Green-Software-Foundation/open19/chapters/book/appendix.adoc

ifndef::imagesdir[:imagesdir: ../../images]

[Appendix]

= Data connector pin assignments

[#table-data-connector-pin-assignments]
.Data connector pin assignments


{sp} +

ifdef::private[]

== Private Appendix

The following material is included for the convenience of Open19 members only. No redistribution to the public is permitted.

=== Data connector sales drawing
[#Molex-Impel-sales-drawing]
.Molex Impel 4x8 Sales Drawing


{sp} +

=== Power connector sales drawing
[#Molex-Ten60-sales-drawing]
.Molex Ten60 Sales DRawing


{sp} +
ifdef::liquid[]
=== Liquid connector spec sheet
[#cpc-blq4-part]
.CPC BLQ4 Spec Sheet


{sp} +

[#cpc-blq6-part]
.CPC BLQ6 Spec Sheet


{sp} +
endif::[]
endif::[]
