Green-Software-Foundation/open19/cooling/single_phase/Max_velocity_stainless.png

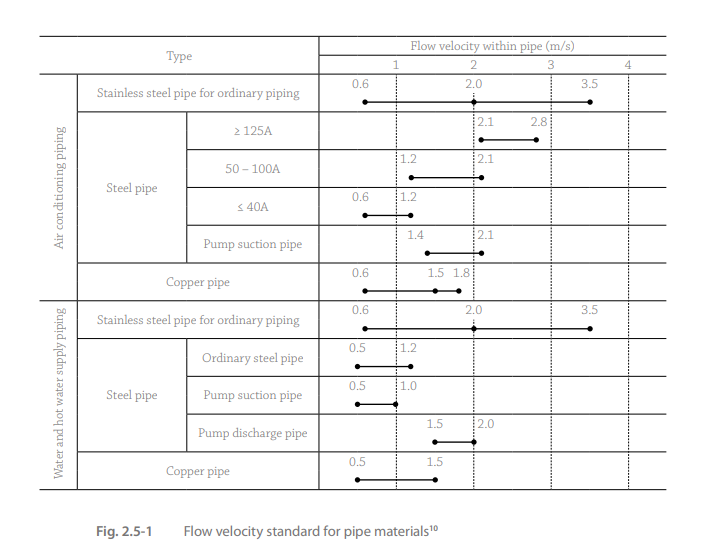
cooling/single_phase/Max_velocity_stainless.png
