Green-Software-Foundation/open19/images/chapters/ch_brick_mechanical/dhdw_brick_mechanical_stop.png

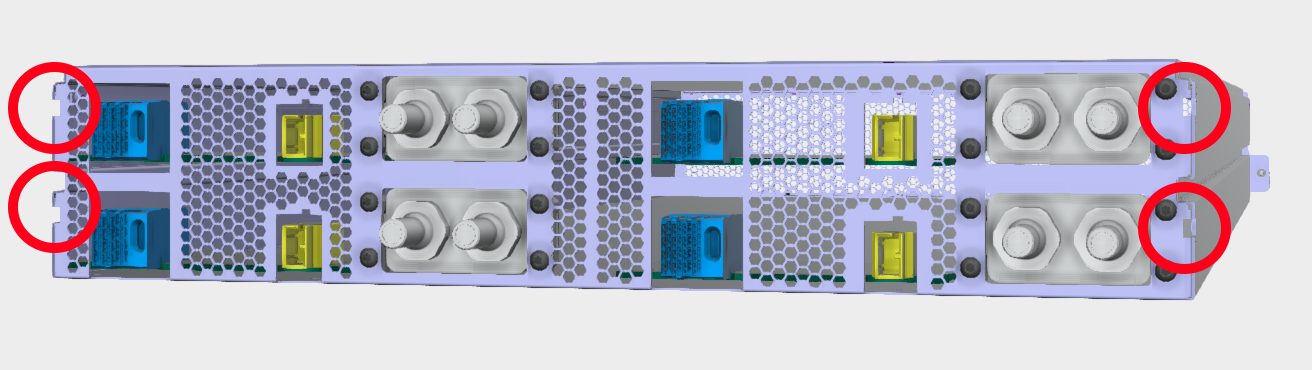
images/chapters/ch_brick_mechanical/dhdw_brick_mechanical_stop.png
