Green-Software-Foundation/open19/images/chapters/ch_brick_mechanical/dhdw_brick_pcb_dimensions.png

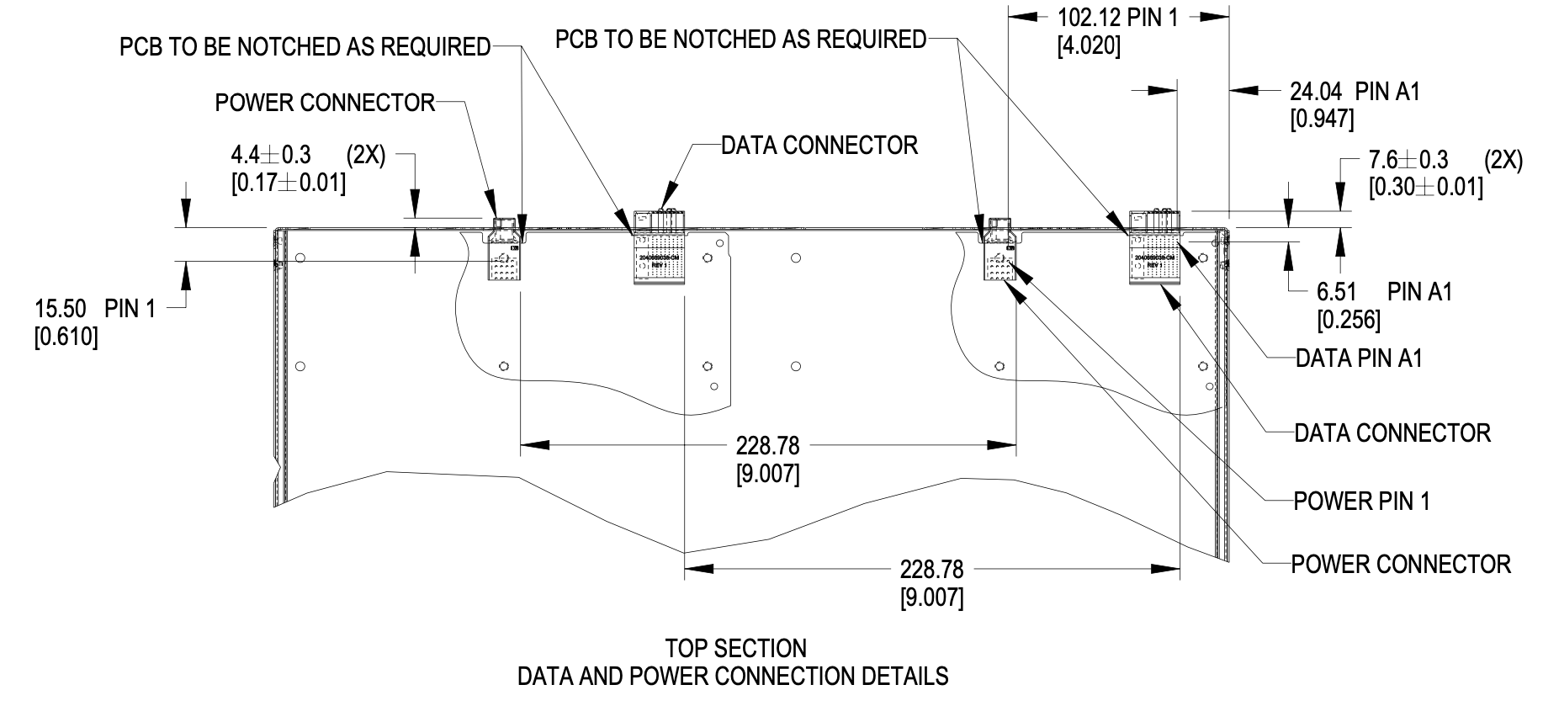
images/chapters/ch_brick_mechanical/dhdw_brick_pcb_dimensions.png
