Green-Software-Foundation/open19/images/chapters/ch_brick_mechanical/dhhw_brick_retention.png

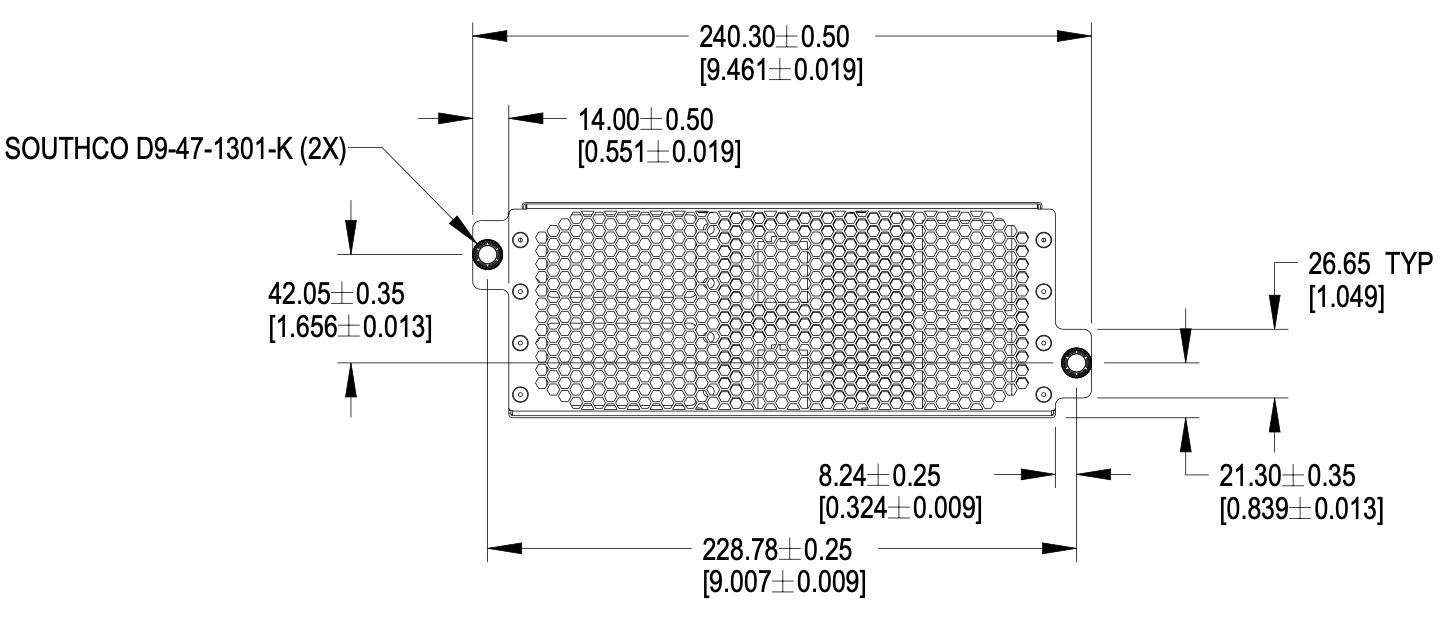
images/chapters/ch_brick_mechanical/dhhw_brick_retention.png
