Green-Software-Foundation/open19/images/chapters/ch_brick_mechanical/shdw_brick_keepout_zone.png

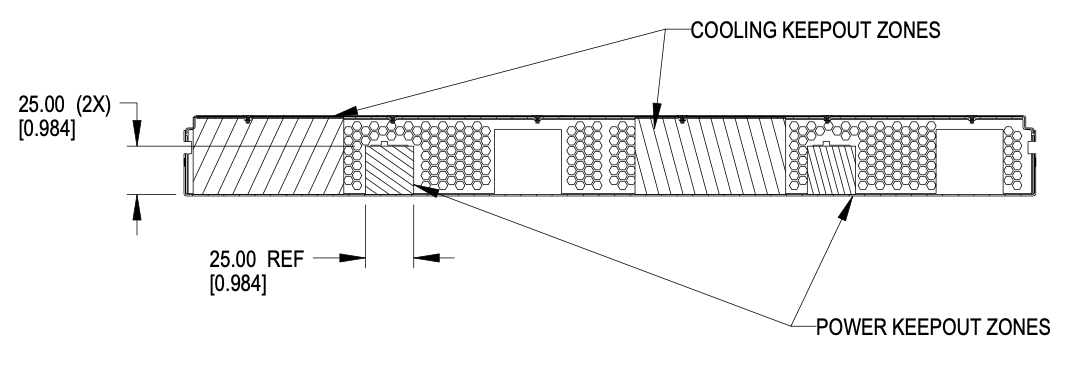
images/chapters/ch_brick_mechanical/shdw_brick_keepout_zone.png
