Green-Software-Foundation/open19/images/chapters/ch_brick_mechanical/shdw_brick_keepout_zone_top.png

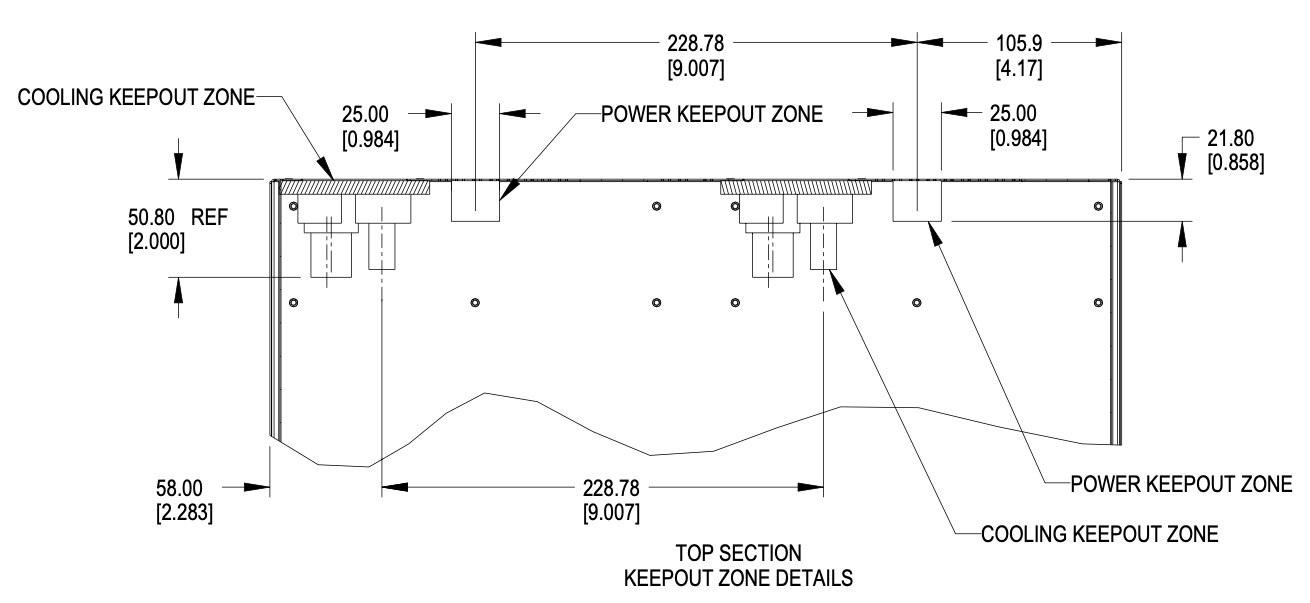
images/chapters/ch_brick_mechanical/shdw_brick_keepout_zone_top.png
