Green-Software-Foundation/open19/images/chapters/ch_brick_mechanical/shdw_brick_keying_dimensions.png

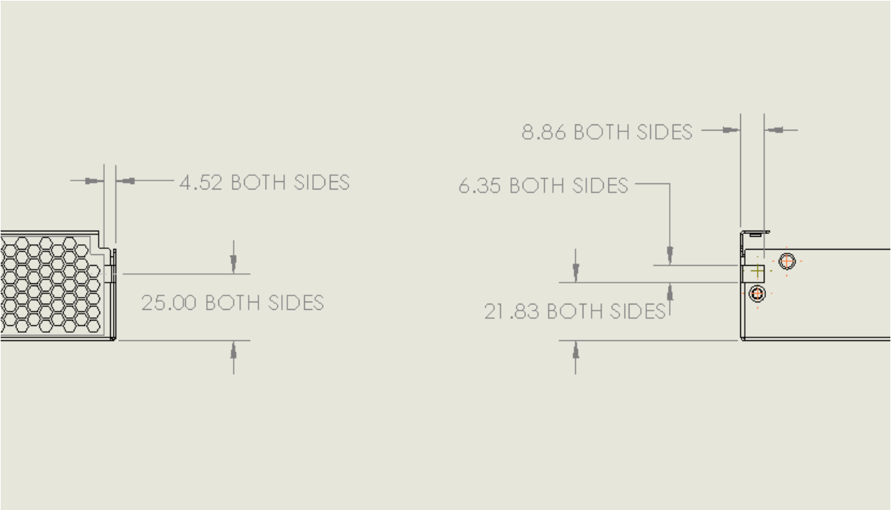
images/chapters/ch_brick_mechanical/shdw_brick_keying_dimensions.png
