Green-Software-Foundation/open19/images/chapters/ch_system_architecture/8rucagefront.png

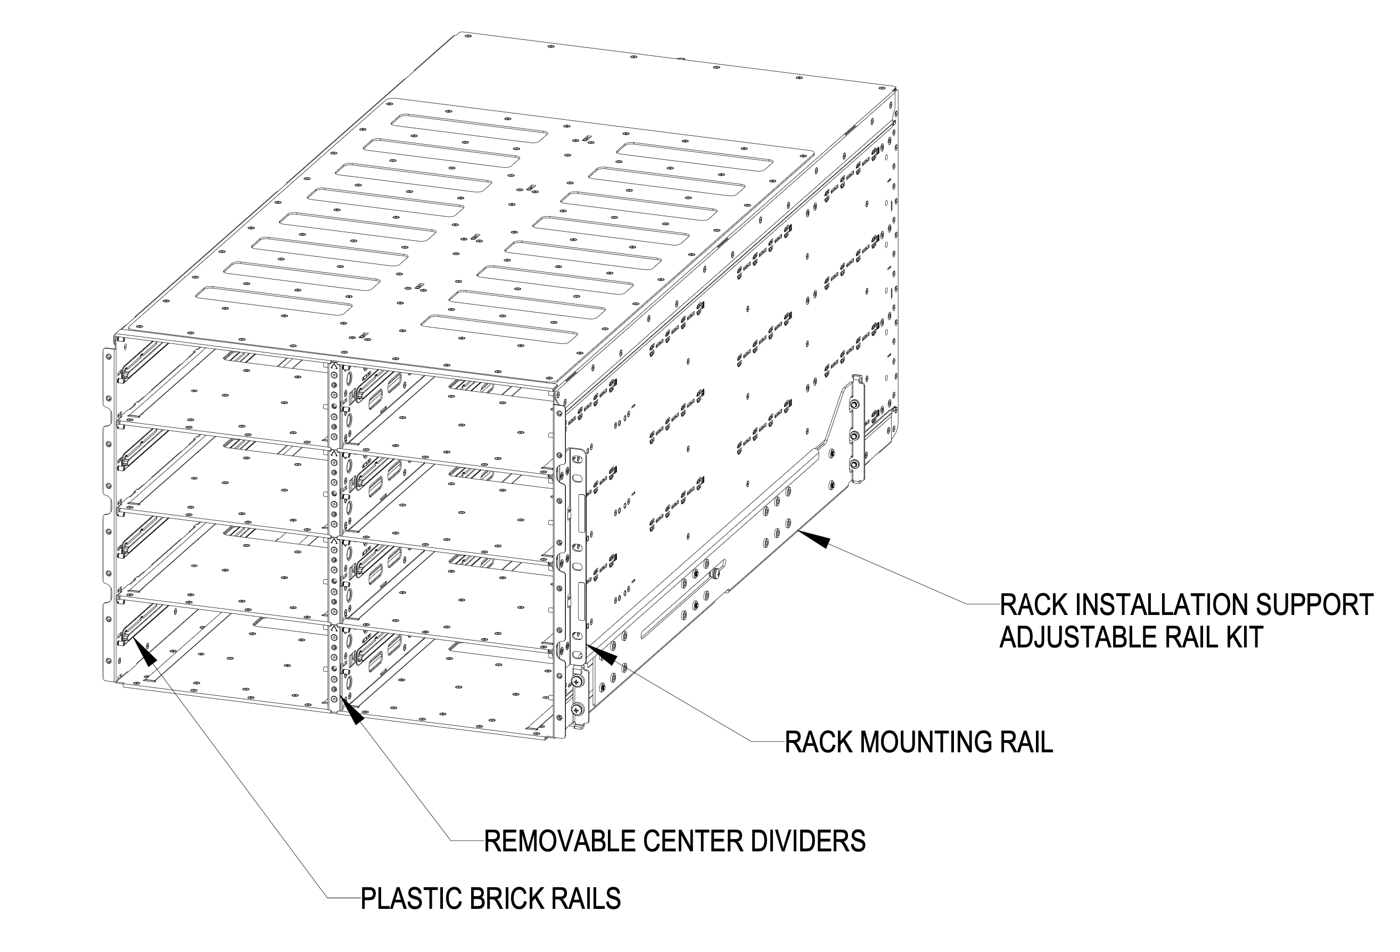
images/chapters/ch_system_architecture/8rucagefront.png
