Green-Software-Foundation/open19/images/chapters/ch_system_architecture/bracket_sample_right.png

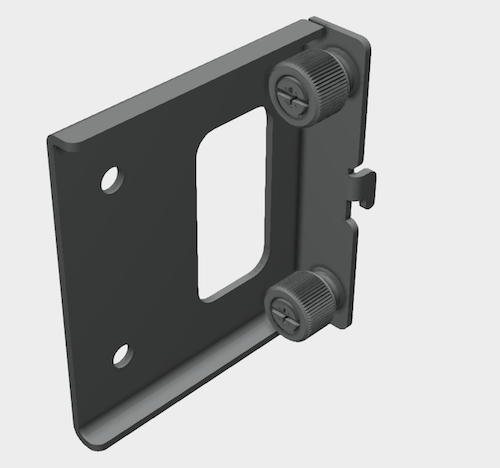
images/chapters/ch_system_architecture/bracket_sample_right.png
