Green-Software-Foundation/open19/images/chapters/ch_system_architecture/cagepaneldetail.png

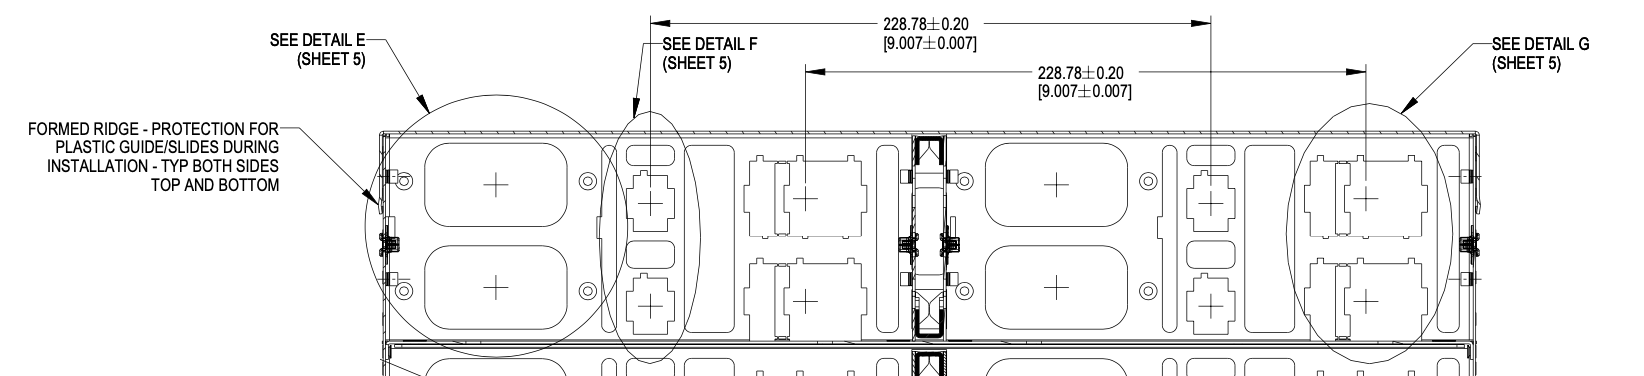
images/chapters/ch_system_architecture/cagepaneldetail.png
