Green-Software-Foundation/open19/images/chapters/ch_system_architecture/center_divider.png

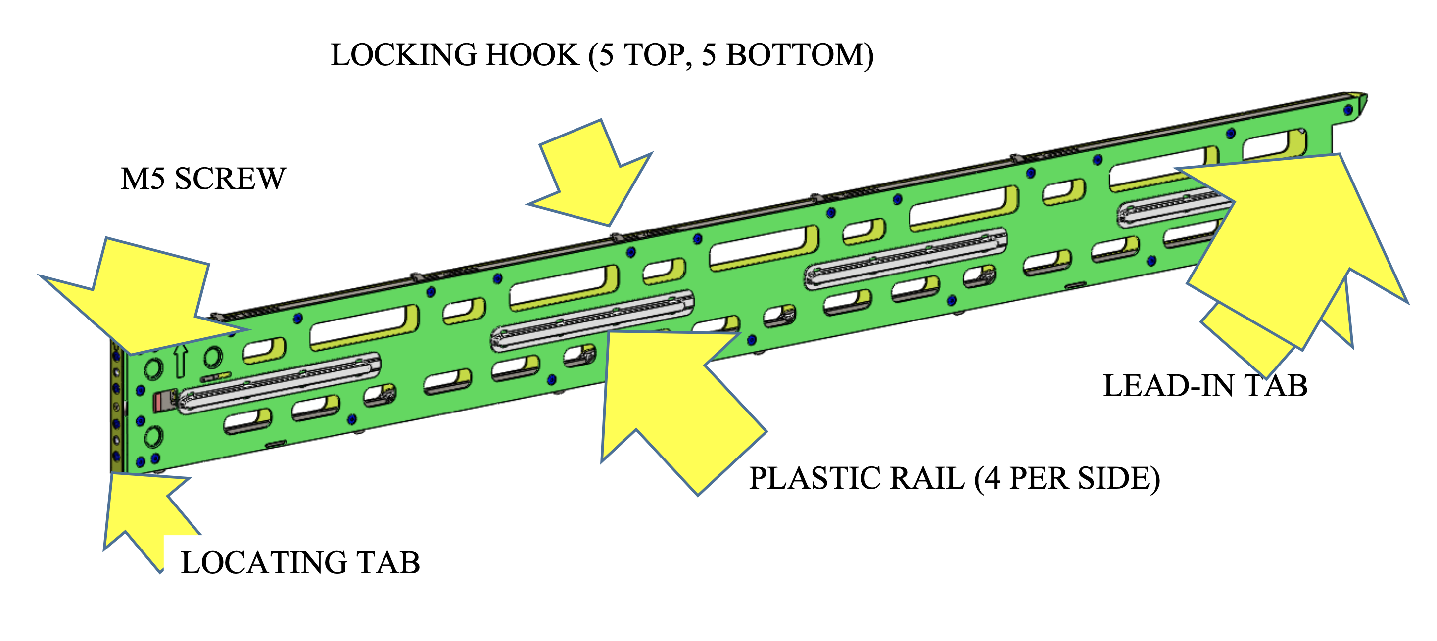
images/chapters/ch_system_architecture/center_divider.png
