Green-Software-Foundation/open19/images/chapters/ch_system_architecture/Coeur_power_shelf_connector.png

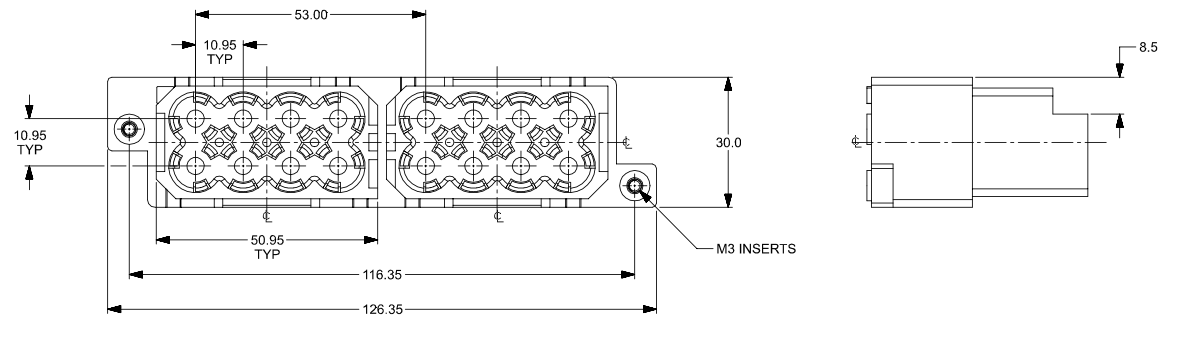
images/chapters/ch_system_architecture/Coeur_power_shelf_connector.png
