Green-Software-Foundation/open19/images/chapters/ch_system_architecture/keying_stops.png

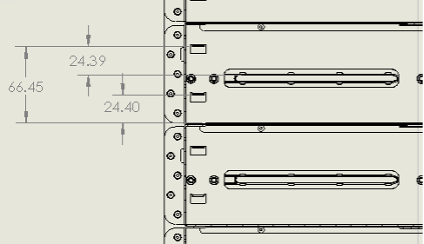
images/chapters/ch_system_architecture/keying_stops.png
