Green-Software-Foundation/open19/images/chapters/ch_system_architecture/open19_v2_cage_horizontal_divider.png

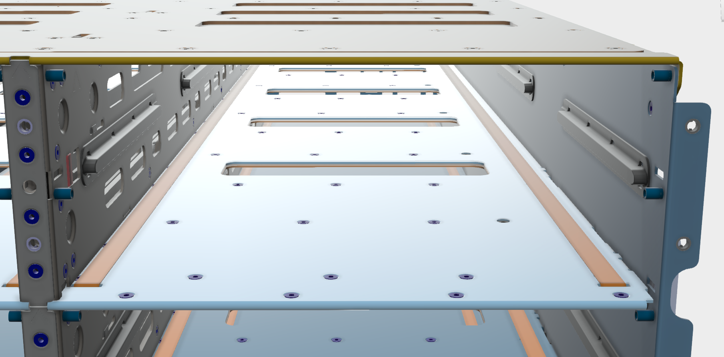
images/chapters/ch_system_architecture/open19_v2_cage_horizontal_divider.png
