Green-Software-Foundation/open19/images/ConfidentialDraft.png

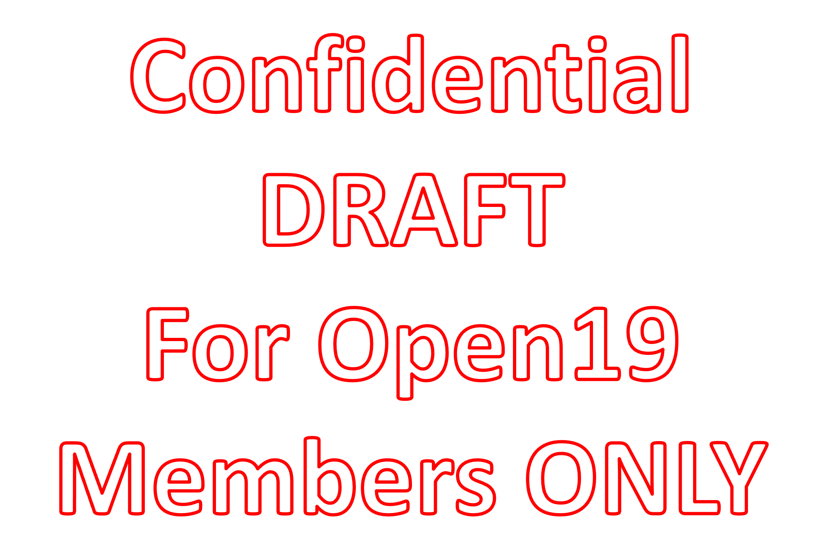
images/ConfidentialDraft.png
