Green-Software-Foundation/open19/images/cooling/single_phase/BLQ4_body.png

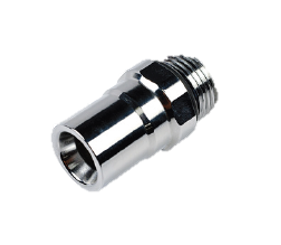
images/cooling/single_phase/BLQ4_body.png
