Green-Software-Foundation/open19/images/cooling/single_phase/BLQ4_flow_vs_dP.png

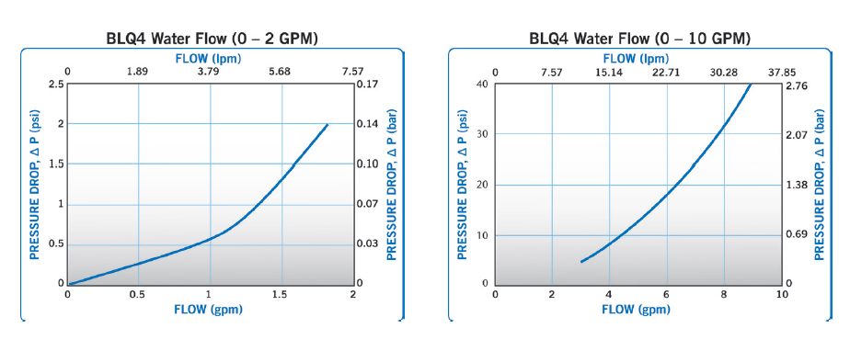
images/cooling/single_phase/BLQ4_flow_vs_dP.png
