Green-Software-Foundation/open19/images/cooling/single_phase/Body_mating_surface.jpg

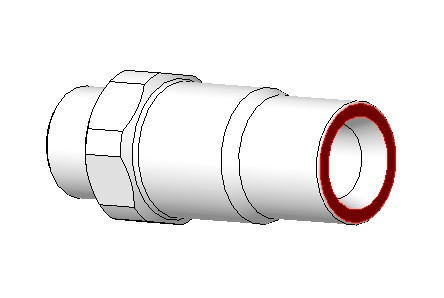
images/cooling/single_phase/Body_mating_surface.jpg
