Green-Software-Foundation/open19/images/cooling/single_phase/brick_offset_dimension.png

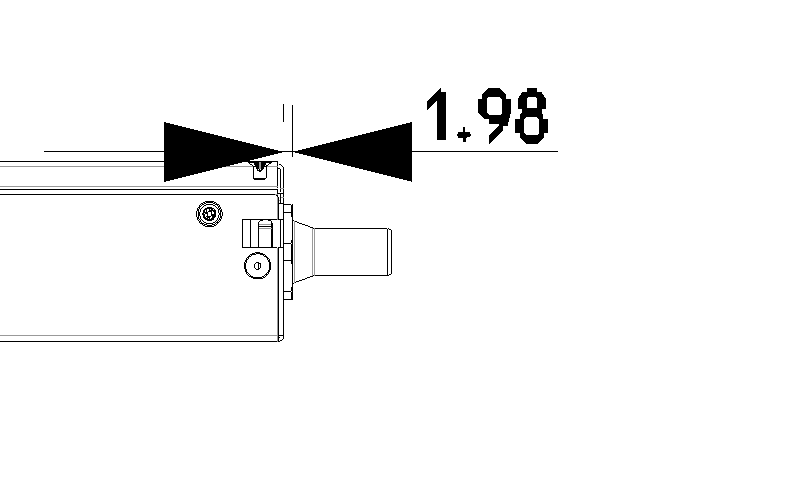
images/cooling/single_phase/brick_offset_dimension.png
