Green-Software-Foundation/open19/images/cooling/single_phase/connector_in_brick_changed_brick.png

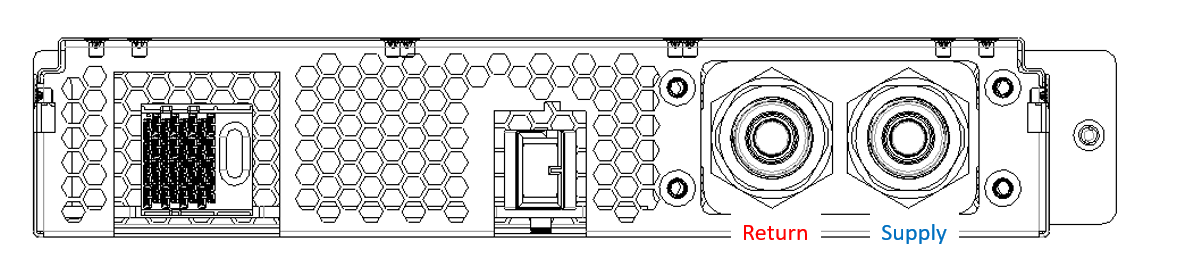
images/cooling/single_phase/connector_in_brick_changed_brick.png
