Green-Software-Foundation/open19/images/cooling/single_phase/no_offset_1p_cage_manifold.png

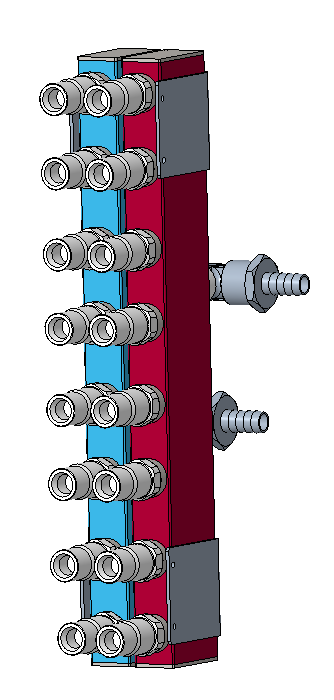
images/cooling/single_phase/no_offset_1p_cage_manifold.png
