Green-Software-Foundation/open19/images/cooling/single_phase/no_offset_brick_connector_dimension.png

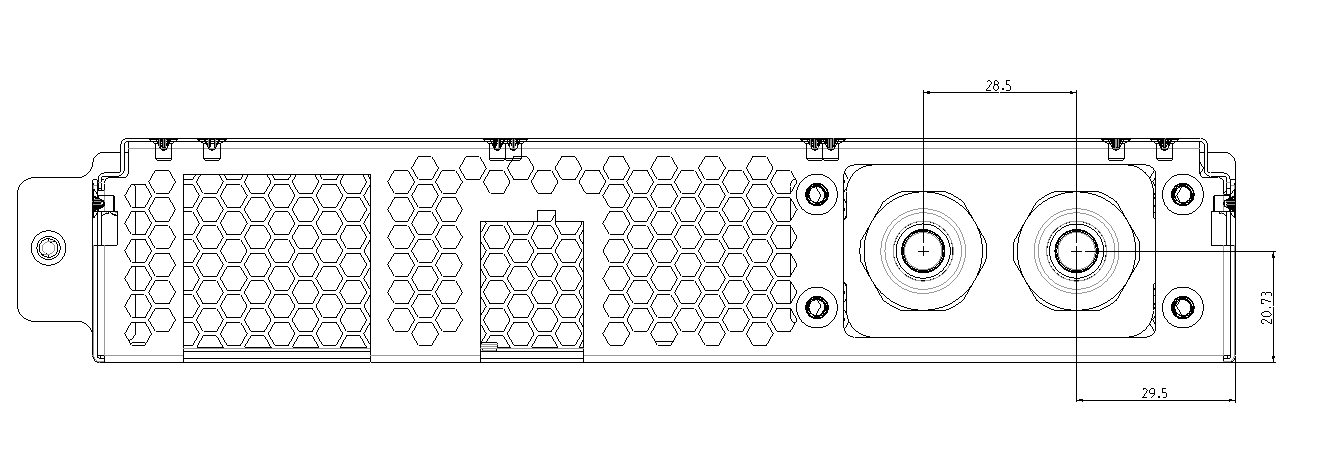
images/cooling/single_phase/no_offset_brick_connector_dimension.png
