Green-Software-Foundation/open19/images/cooling/single_phase/no_offset_brick_supply_return.png

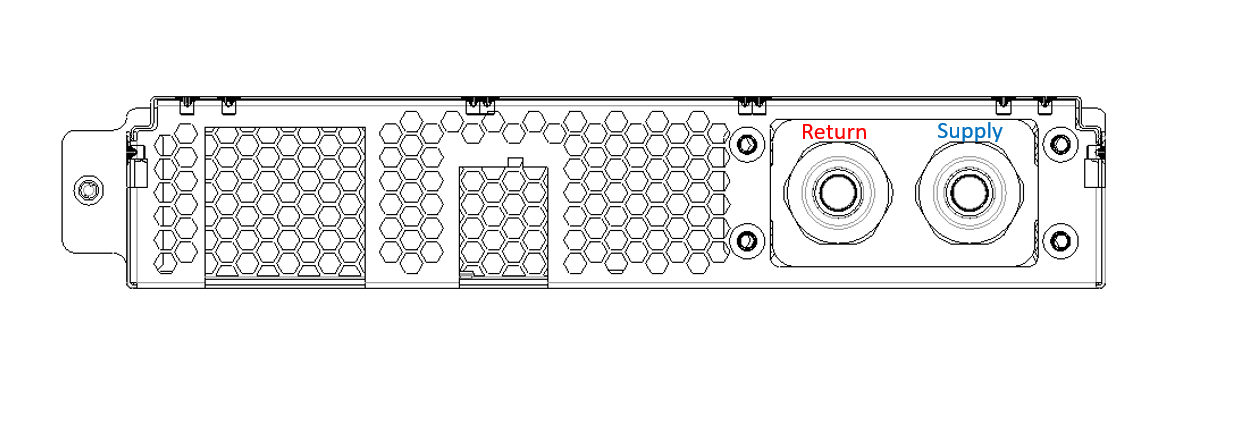
images/cooling/single_phase/no_offset_brick_supply_return.png
