Green-Software-Foundation/open19/images/cooling/single_phase/No_offset_cage_with_manifold_1pbrick.png

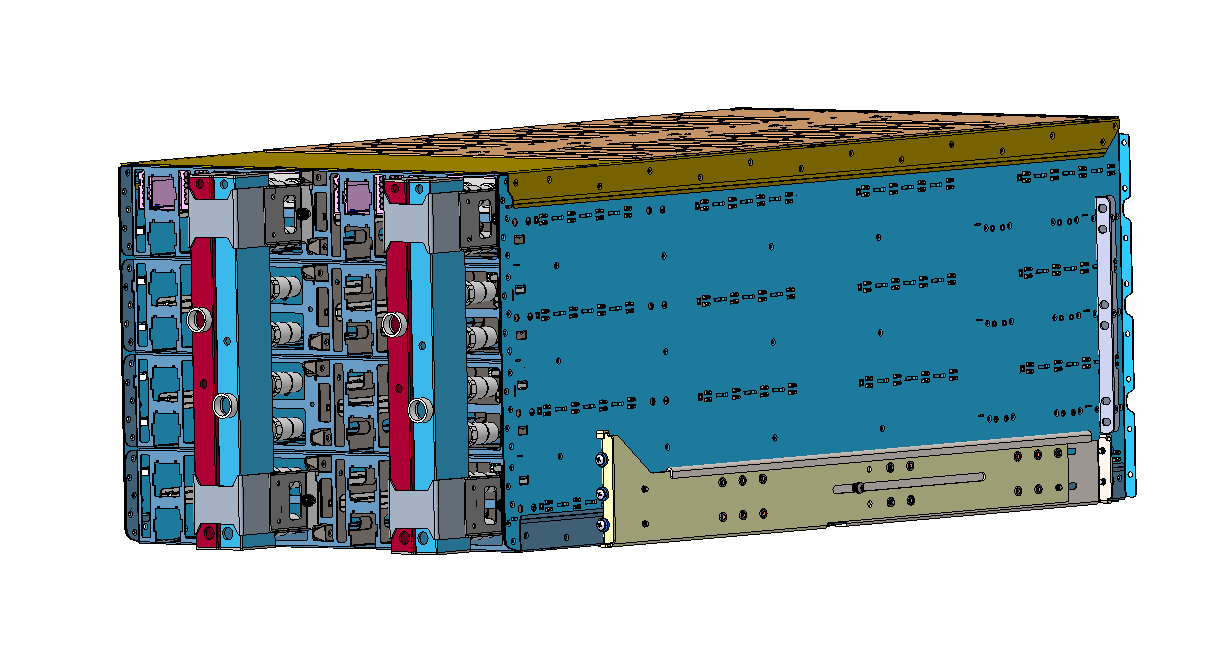
images/cooling/single_phase/No_offset_cage_with_manifold_1pbrick.png
