Green-Software-Foundation/open19/images/cooling/single_phase/no_offset_manifold_spacing.png

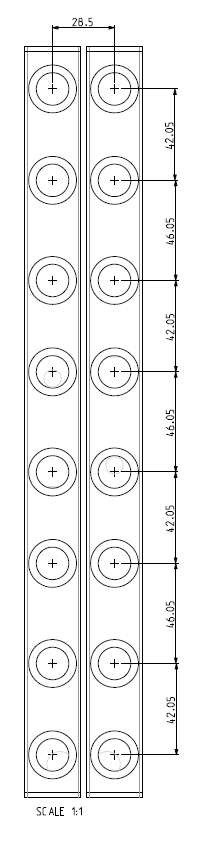
images/cooling/single_phase/no_offset_manifold_spacing.png
