Green-Software-Foundation/open19/images/cooling/single_phase/shdw_connector_in_brick.png

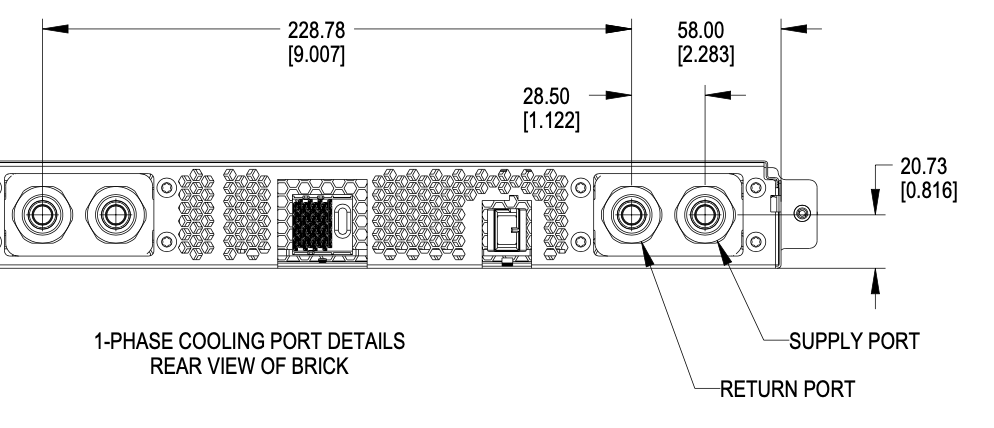
images/cooling/single_phase/shdw_connector_in_brick.png
