Green-Software-Foundation/open19/images/cooling/two_phase/dhhw_supply_return_dimensions.png

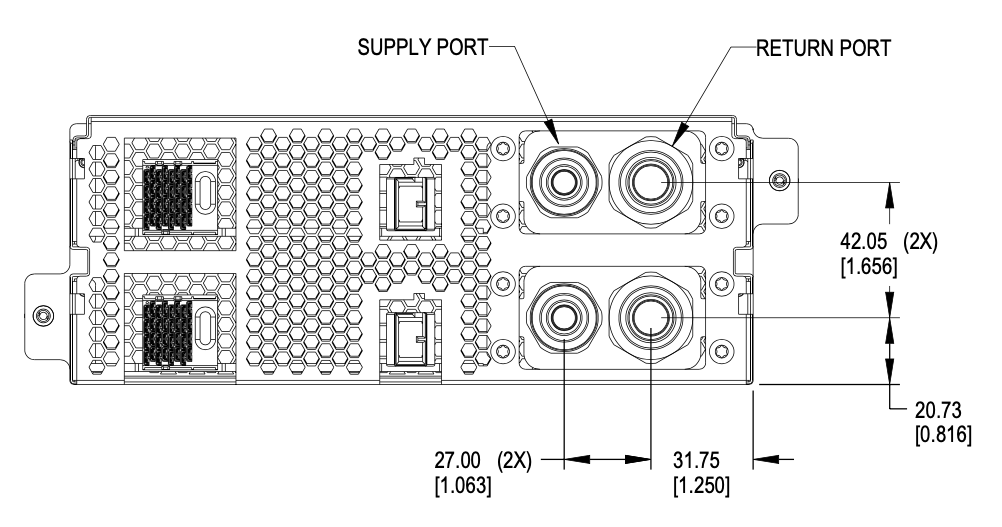
images/cooling/two_phase/dhhw_supply_return_dimensions.png
