Green-Software-Foundation/open19/images/cooling/two_phase/image1.png

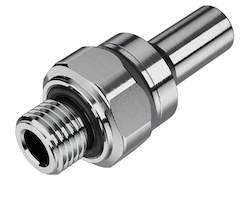
images/cooling/two_phase/image1.png
