Green-Software-Foundation/open19/images/cooling/two_phase/image3.png

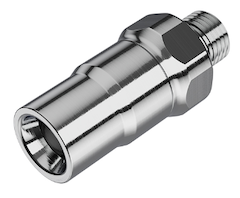
images/cooling/two_phase/image3.png
