Green-Software-Foundation/open19/images/cooling/two_phase/image5.png

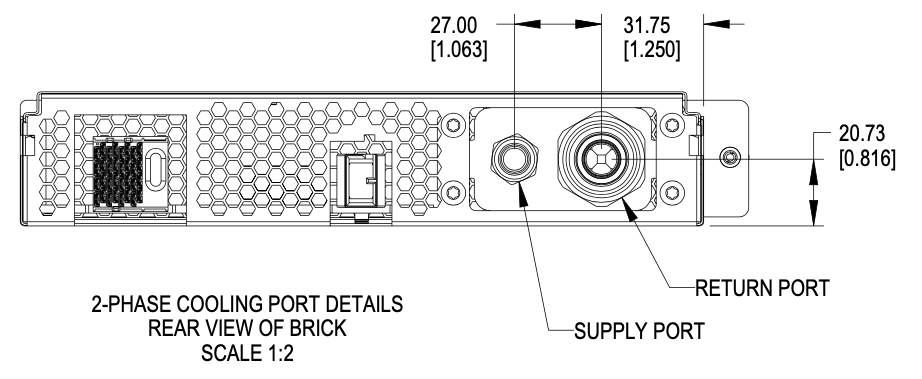
images/cooling/two_phase/image5.png
