Green-Software-Foundation/open19/images/cooling/two_phase/image8.png

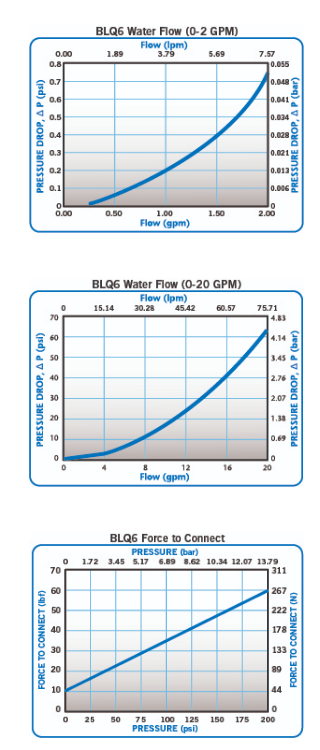
images/cooling/two_phase/image8.png
