Green-Software-Foundation/open19/images/cooling/two_phase/image9.png

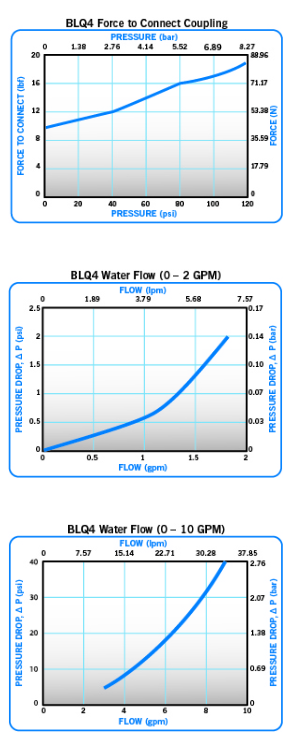
images/cooling/two_phase/image9.png
