Green-Software-Foundation/open19/images/cooling/two_phase/image10.png

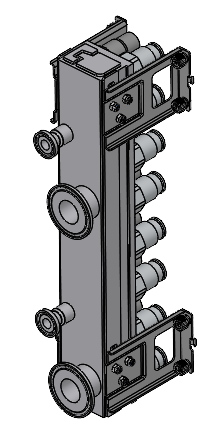
images/cooling/two_phase/image10.png
