Green-Software-Foundation/open19/images/cooling/two_phase/image11.png

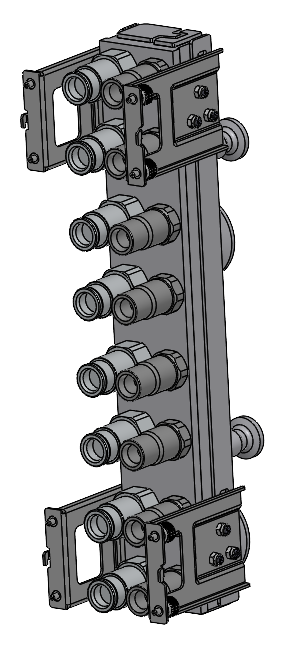
images/cooling/two_phase/image11.png
