Green-Software-Foundation/open19/images/cooling/two_phase/image12.png

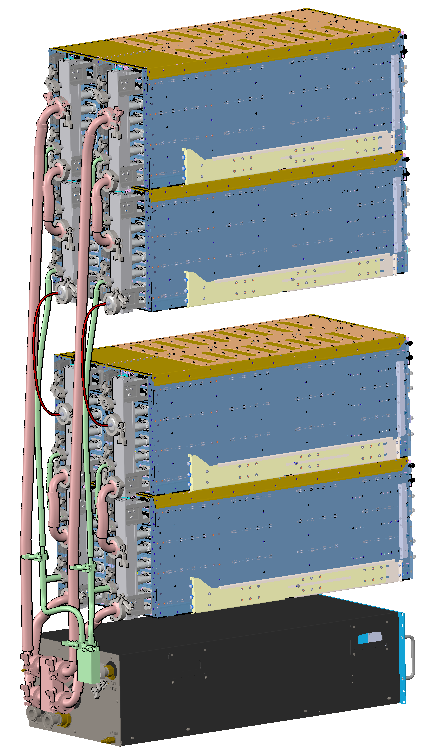
images/cooling/two_phase/image12.png
