Green-Software-Foundation/open19/images/cooling/two_phase/imagea8.png

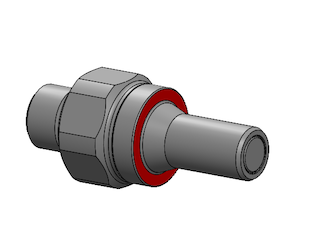
images/cooling/two_phase/imagea8.png
