Green-Software-Foundation/open19/images/cooling/two_phase/imagea9.png

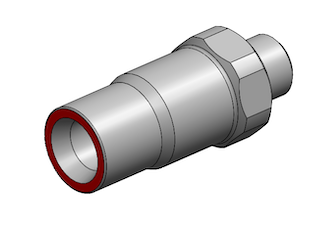
images/cooling/two_phase/imagea9.png
