Green-Software-Foundation/open19/images/cooling/two_phase/imagea11.png

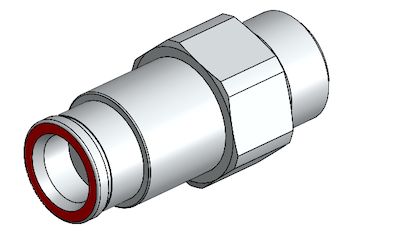
images/cooling/two_phase/imagea11.png
