Green-Software-Foundation/open19/images/cooling/two_phase/imagea12.png

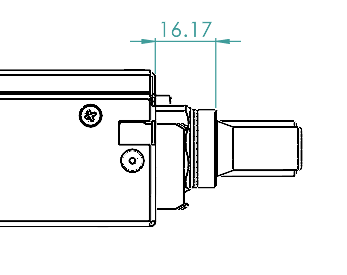
images/cooling/two_phase/imagea12.png
