Green-Software-Foundation/open19/images/cooling/two_phase/imagea13.png

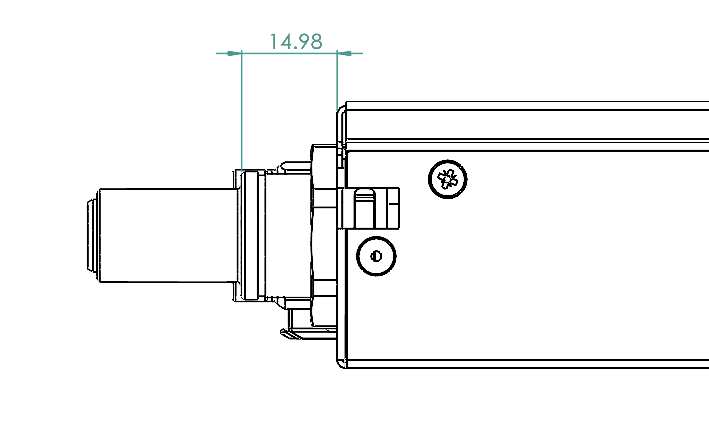
images/cooling/two_phase/imagea13.png
