Green-Software-Foundation/open19/images/cooling/two_phase/shdw_supply_return_dimensions.png

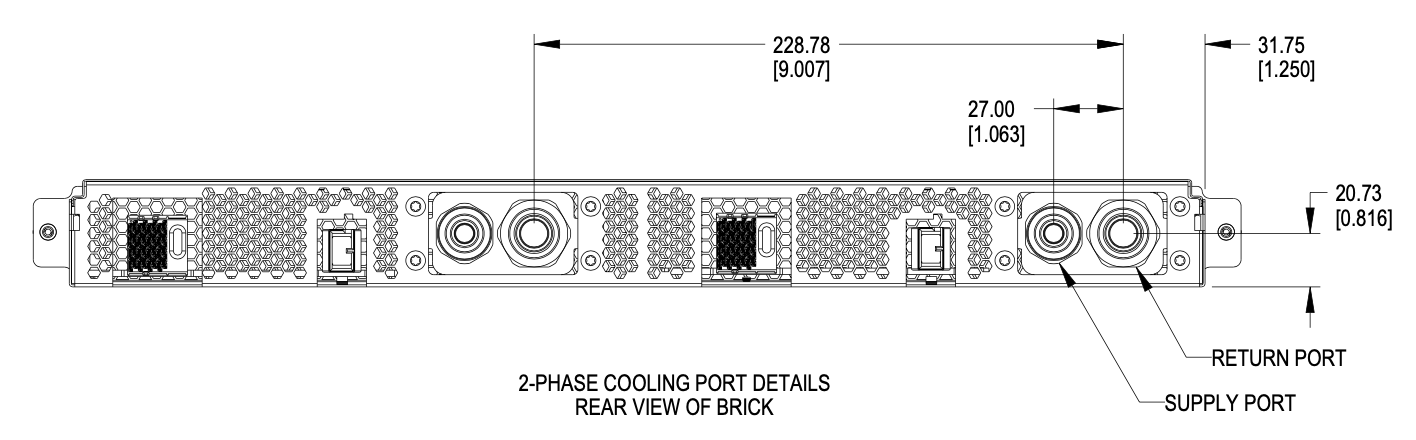
images/cooling/two_phase/shdw_supply_return_dimensions.png
