Green-Software-Foundation/open19/images/cooling/unified/shhw_brick_cutout.png

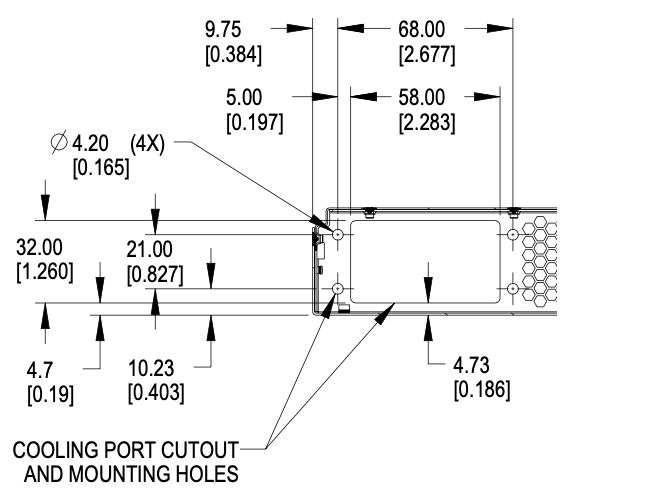
images/cooling/unified/shhw_brick_cutout.png
