Green-Software-Foundation/open19/images/data/Impel_Open19V2_4x8_Mated.png

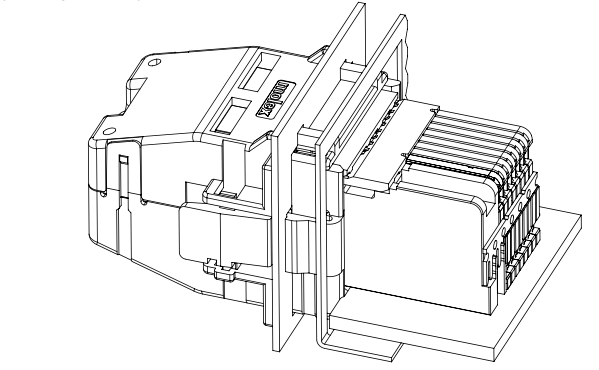
images/data/Impel_Open19V2_4x8_Mated.png
