Green-Software-Foundation/open19/images/Figure 1 - Rack Level Open19 Platform Overview.jpg

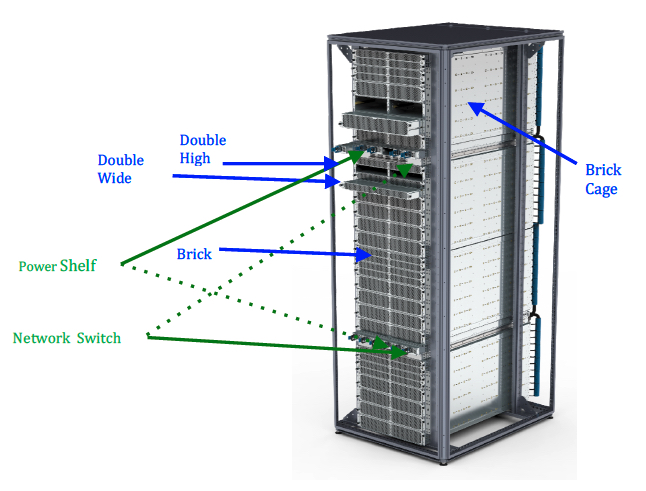
images/Figure 1 - Rack Level Open19 Platform Overview.jpg
