Green-Software-Foundation/open19/images/Figure 2 - Brick Dimensions.png

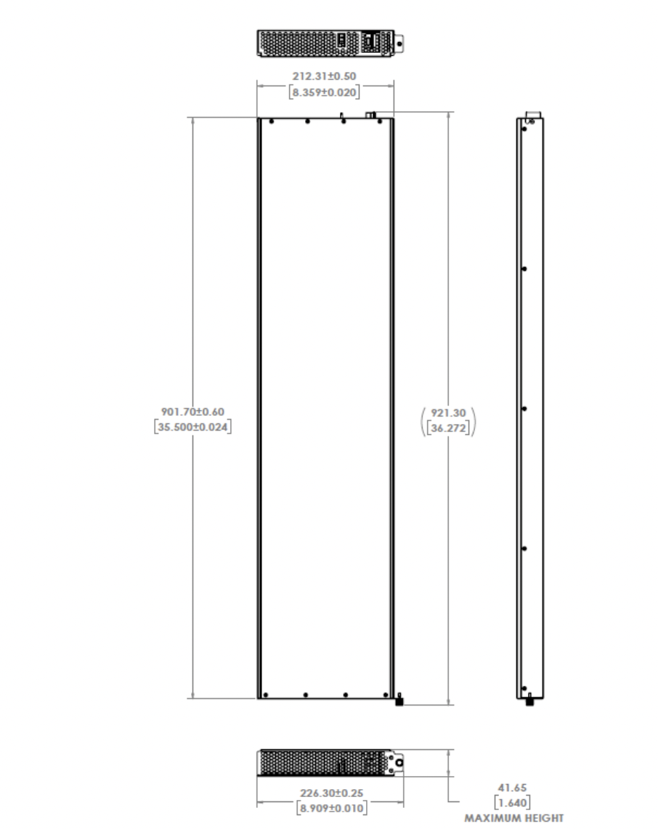
images/Figure 2 - Brick Dimensions.png
