Green-Software-Foundation/open19/images/Figure 4 - Brick PCB Dimensions.jpg

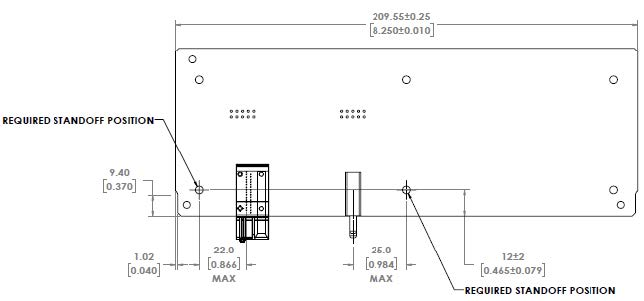
images/Figure 4 - Brick PCB Dimensions.jpg
