Green-Software-Foundation/open19/images/Figure 5 - PCB Connectors.jpg

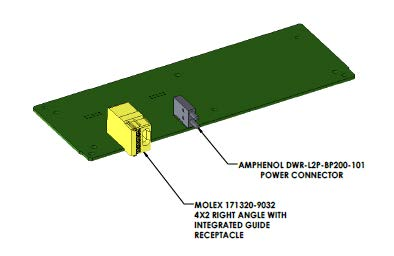
images/Figure 5 - PCB Connectors.jpg
