Green-Software-Foundation/open19/images/Figure 6 - Brick PCB Overall Dimensions.jpg

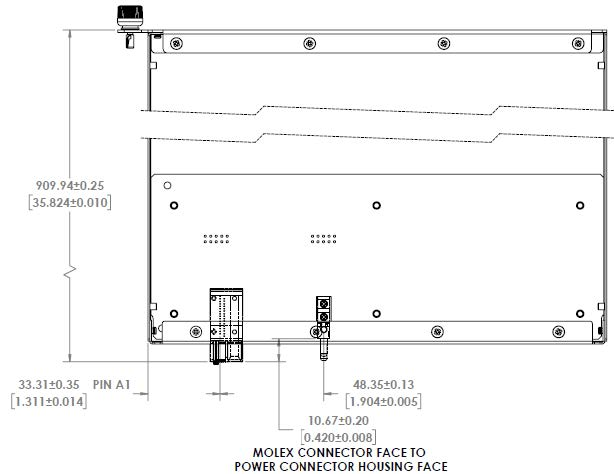
images/Figure 6 - Brick PCB Overall Dimensions.jpg
