Green-Software-Foundation/open19/images/Figure 7 - Brick PCBA Pinout Definition.jpg

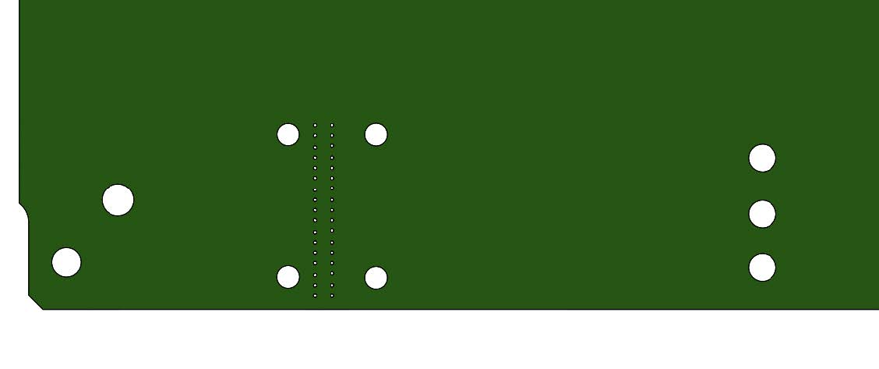
images/Figure 7 - Brick PCBA Pinout Definition.jpg
