Green-Software-Foundation/open19/images/Figure 7 - Brick PCBA Pinout Definition.png

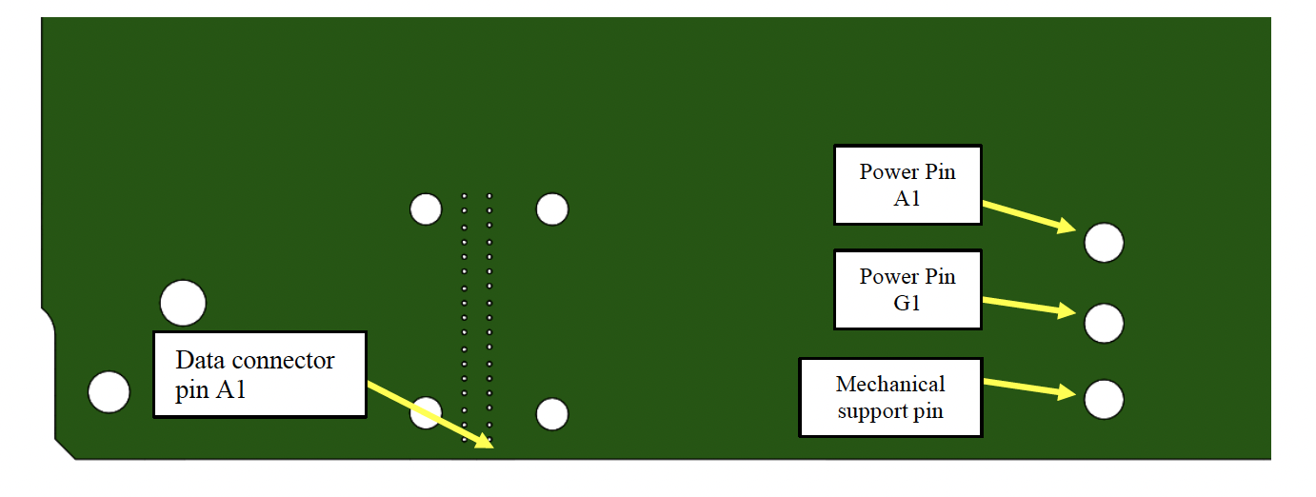
images/Figure 7 - Brick PCBA Pinout Definition.png
