Green-Software-Foundation/open19/images/Figure 8 - Brick Retention.jpg

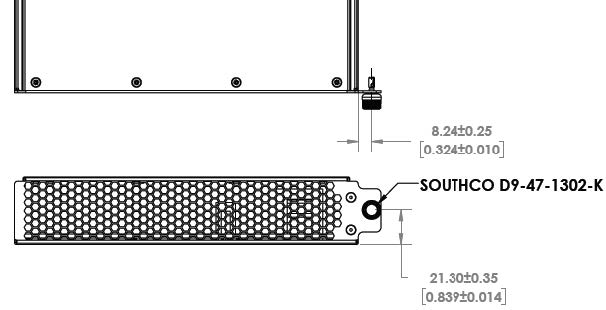
images/Figure 8 - Brick Retention.jpg
