Green-Software-Foundation/open19/images/Figure 9 - Brick Design Consideration.jpg

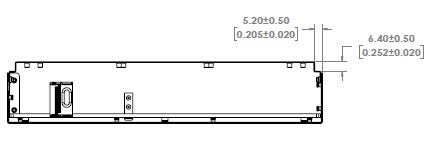
images/Figure 9 - Brick Design Consideration.jpg
