Green-Software-Foundation/open19/images/Figure 14 - 3D Brick Keying.jpg

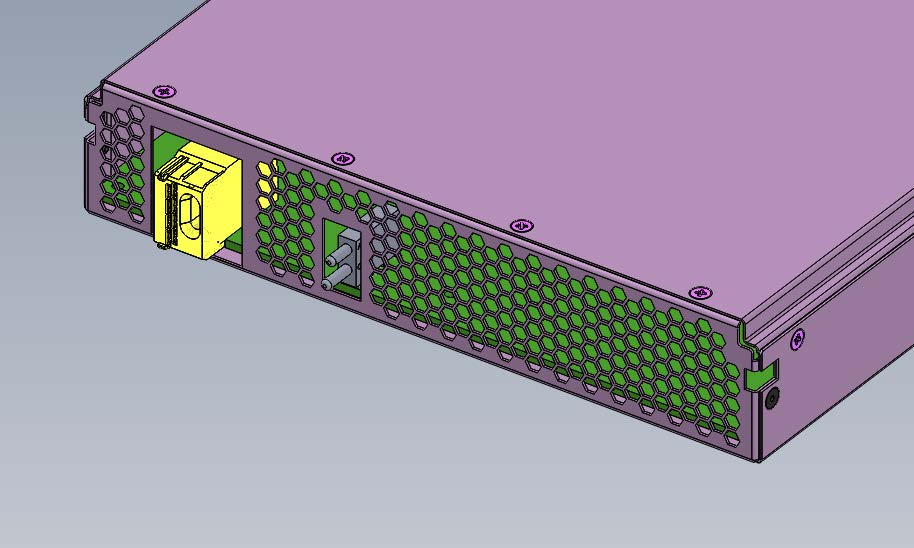
images/Figure 14 - 3D Brick Keying.jpg
