Green-Software-Foundation/open19/images/Figure 17 - Double Wide Brick PCB Dimensions.jpg

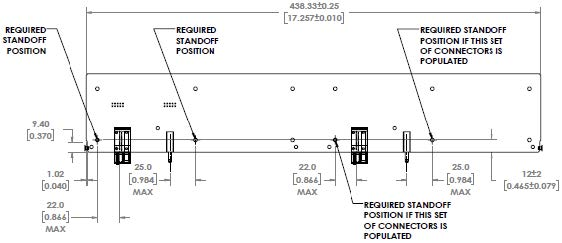
images/Figure 17 - Double Wide Brick PCB Dimensions.jpg
