Green-Software-Foundation/open19/images/Figure 20 - Double Wide Brick PCBA Pinout Definition.png

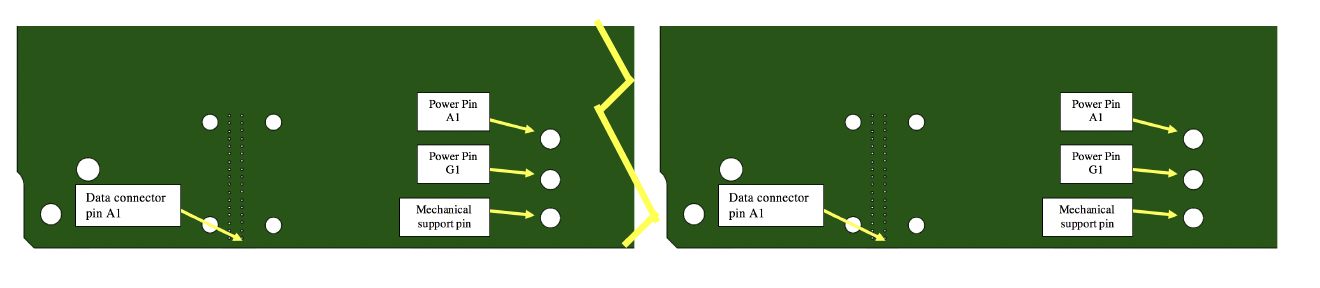
images/Figure 20 - Double Wide Brick PCBA Pinout Definition.png
