Green-Software-Foundation/open19/images/Figure 22 - Double Wide Brick Design Consideration.jpg

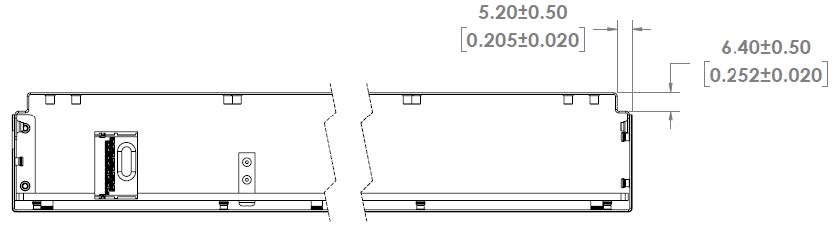
images/Figure 22 - Double Wide Brick Design Consideration.jpg
