Green-Software-Foundation/open19/images/Figure 24 - Double Wide Brick Faceplate.jpg

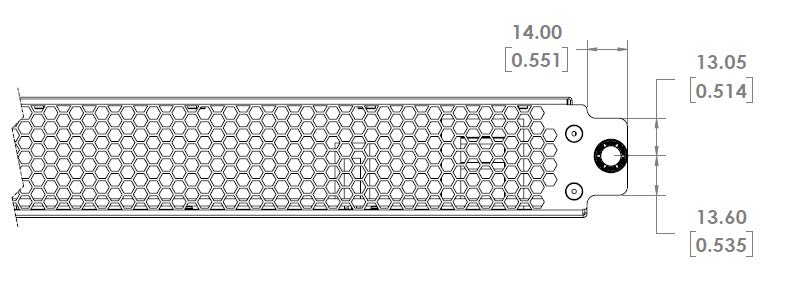
images/Figure 24 - Double Wide Brick Faceplate.jpg
