Green-Software-Foundation/open19/images/Figure 27 - Full Width Brick Keying Location .jpg

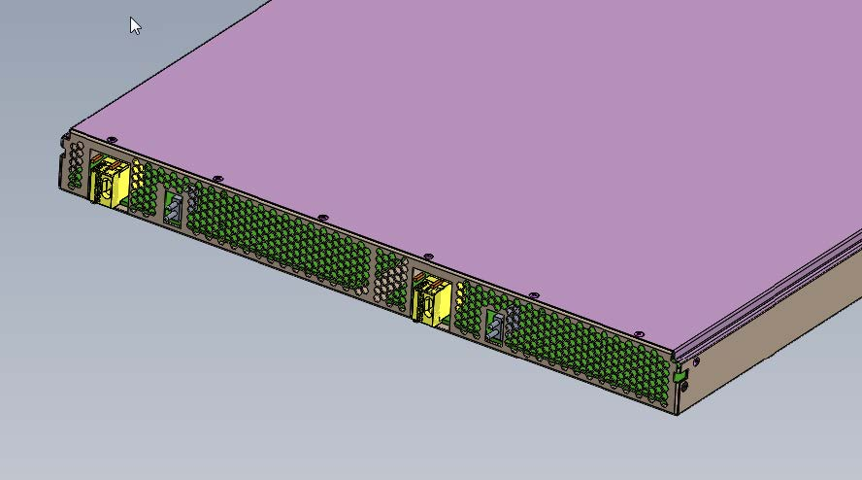
images/Figure 27 - Full Width Brick Keying Location .jpg
