Green-Software-Foundation/open19/images/Figure 28 - Double High Half Width Brick Dimensions.jpg

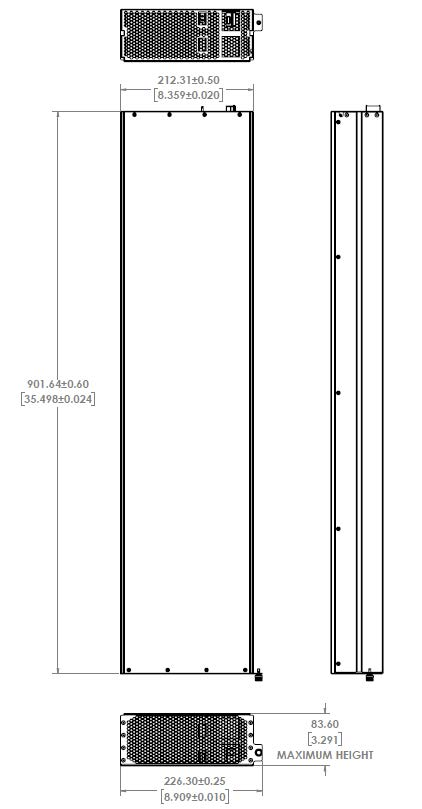
images/Figure 28 - Double High Half Width Brick Dimensions.jpg
