Green-Software-Foundation/open19/images/Figure 29 - DWHW Brick Main PCBA.jpg

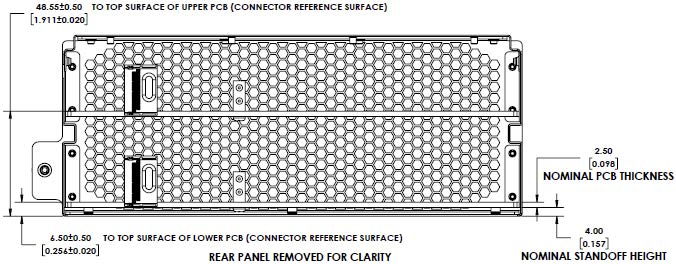
images/Figure 29 - DWHW Brick Main PCBA.jpg
