Green-Software-Foundation/open19/images/Figure 33 - Double Wide Brick PCBA Pinout Definition.png

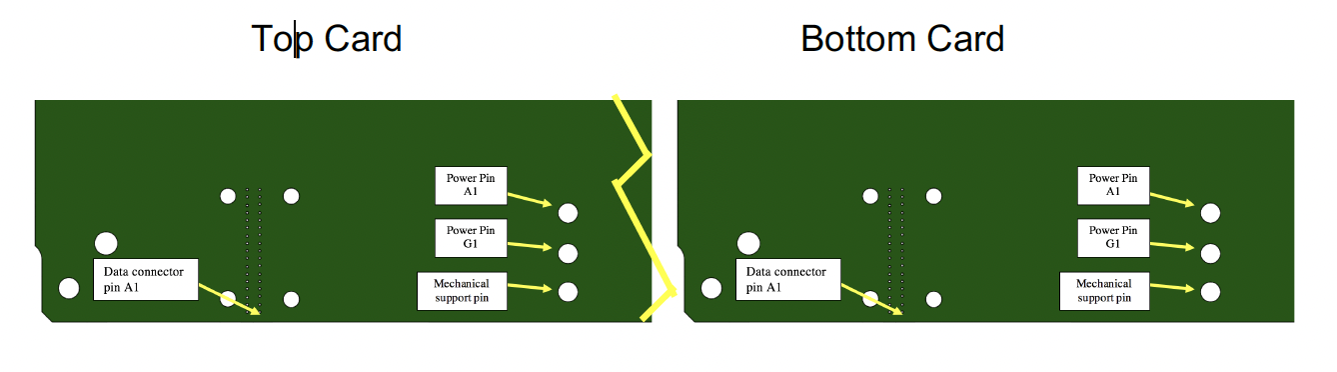
images/Figure 33 - Double Wide Brick PCBA Pinout Definition.png
