Green-Software-Foundation/open19/images/Figure 34 - Double High Half Width Brick Retention.jpg

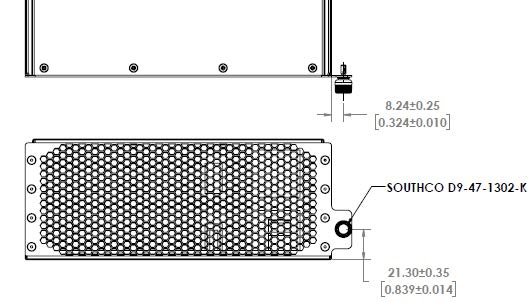
images/Figure 34 - Double High Half Width Brick Retention.jpg
