Green-Software-Foundation/open19/images/Figure 35 - Double High Half Width Brick Retention.png

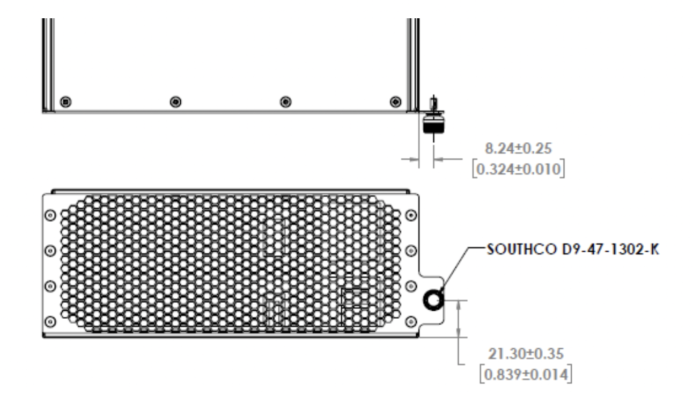
images/Figure 35 - Double High Half Width Brick Retention.png
