Green-Software-Foundation/open19/images/Figure 36 - Double High Half Width Brick Faceplate2.jpg

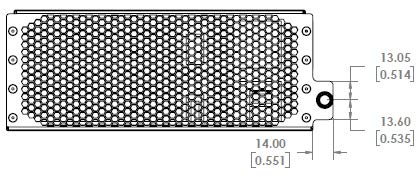
images/Figure 36 - Double High Half Width Brick Faceplate2.jpg
