Green-Software-Foundation/open19/images/Figure 37 - Half Width Double High Brick Keying Dimensions.jpg

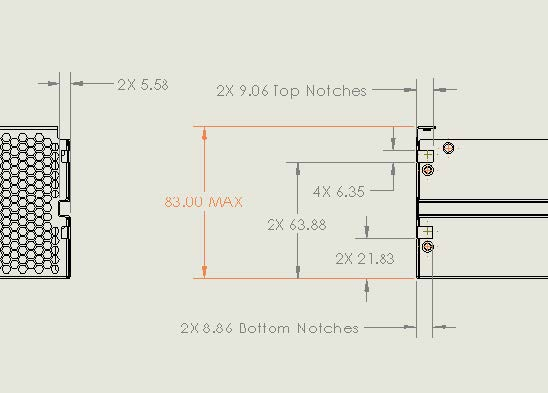
images/Figure 37 - Half Width Double High Brick Keying Dimensions.jpg
