Green-Software-Foundation/open19/images/Figure 39 - Full Width Brick Keying Location.jpg

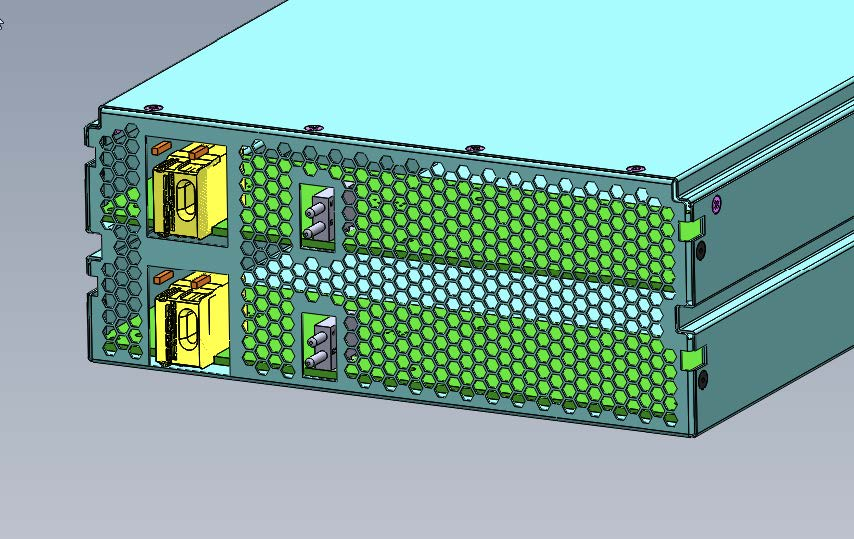
images/Figure 39 - Full Width Brick Keying Location.jpg
