Green-Software-Foundation/open19/images/Figure 41 - Double Wide Double High Brick Dimensions.jpg

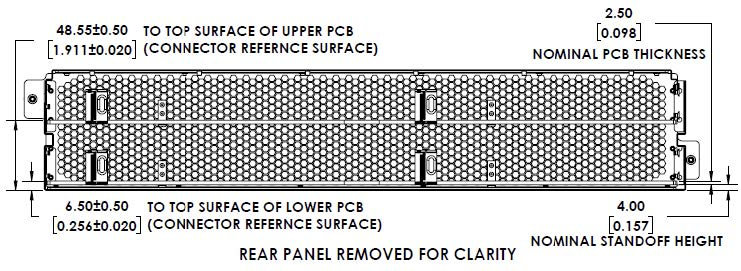
images/Figure 41 - Double Wide Double High Brick Dimensions.jpg
