Green-Software-Foundation/open19/images/Figure 44 - Double Wide Double High Brick PCB Overall Dimensions.png

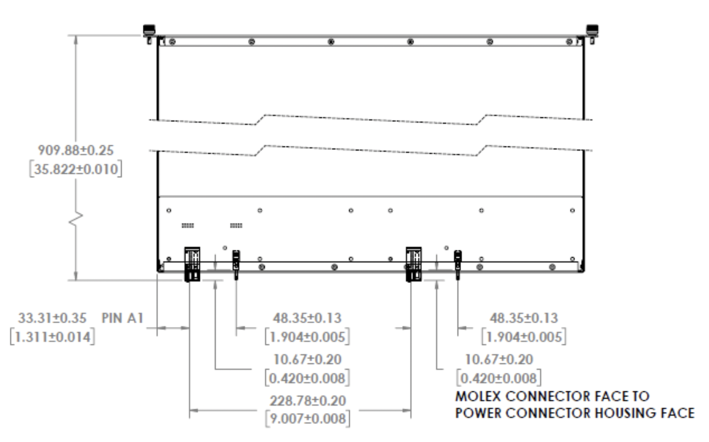
images/Figure 44 - Double Wide Double High Brick PCB Overall Dimensions.png
