Green-Software-Foundation/open19/images/Figure 45 - Double Wide Double High Brick PCBA Pinout Definition.png

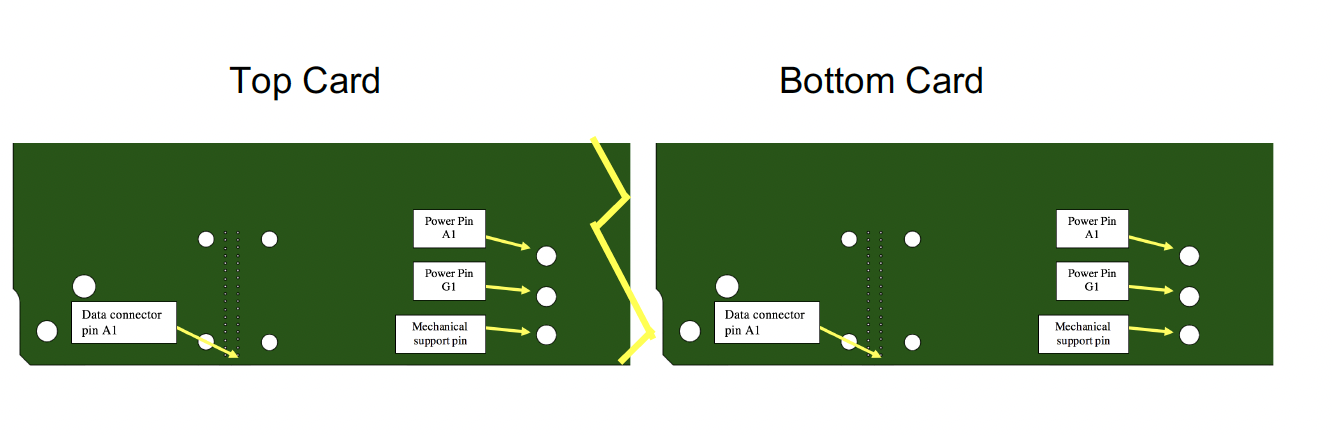
images/Figure 45 - Double Wide Double High Brick PCBA Pinout Definition.png
