Green-Software-Foundation/open19/images/Figure 46 - Double High Double Wide Brick Retention.png

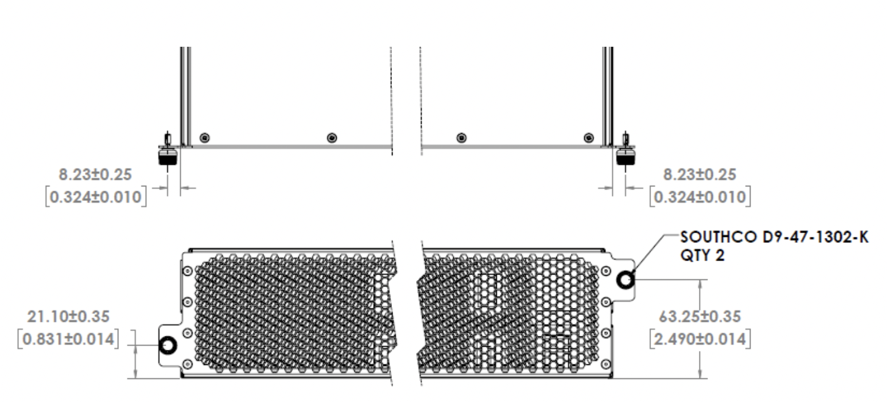
images/Figure 46 - Double High Double Wide Brick Retention.png
