Green-Software-Foundation/open19/images/Figure 46 - Double Wide Double High Brick PCBA Pinout Definition.png

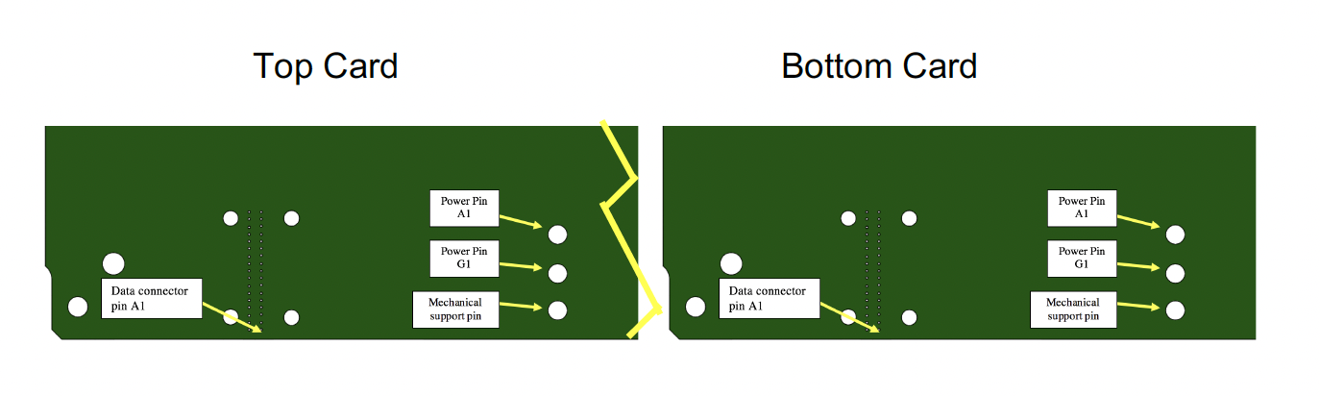
images/Figure 46 - Double Wide Double High Brick PCBA Pinout Definition.png
