Green-Software-Foundation/open19/images/Figure 47 - Double High Double Wide Brick Faceplate 1.jpg

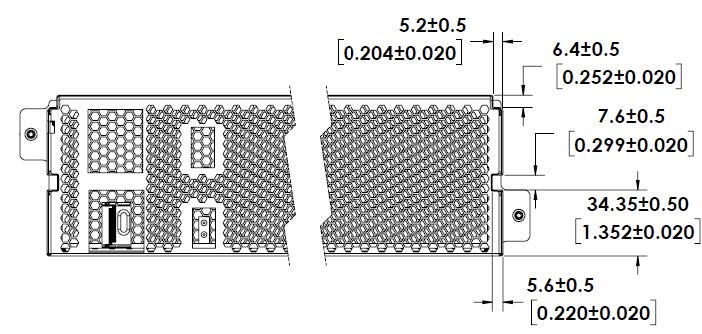
images/Figure 47 - Double High Double Wide Brick Faceplate 1.jpg
