Green-Software-Foundation/open19/images/Figure 48 - Double High Double Wide Brick Faceplate 2.jpg

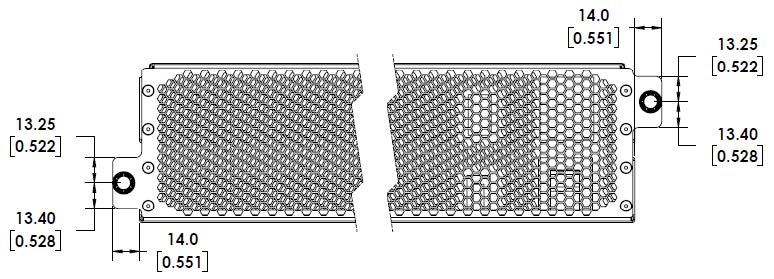
images/Figure 48 - Double High Double Wide Brick Faceplate 2.jpg
