Green-Software-Foundation/open19/images/Figure 51 - Double High Double Wide Brick Design Consideration 3D.jpg

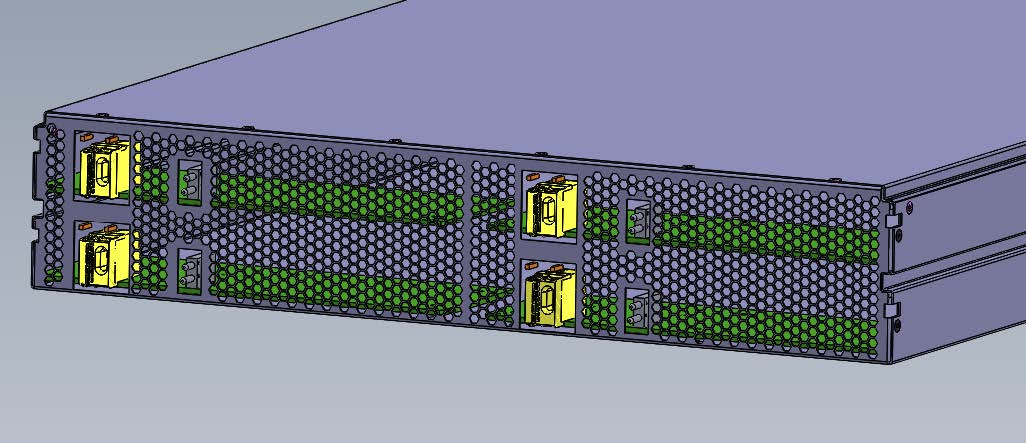
images/Figure 51 - Double High Double Wide Brick Design Consideration 3D.jpg
