Green-Software-Foundation/open19/images/power/brick_power_connector_panel_location.png

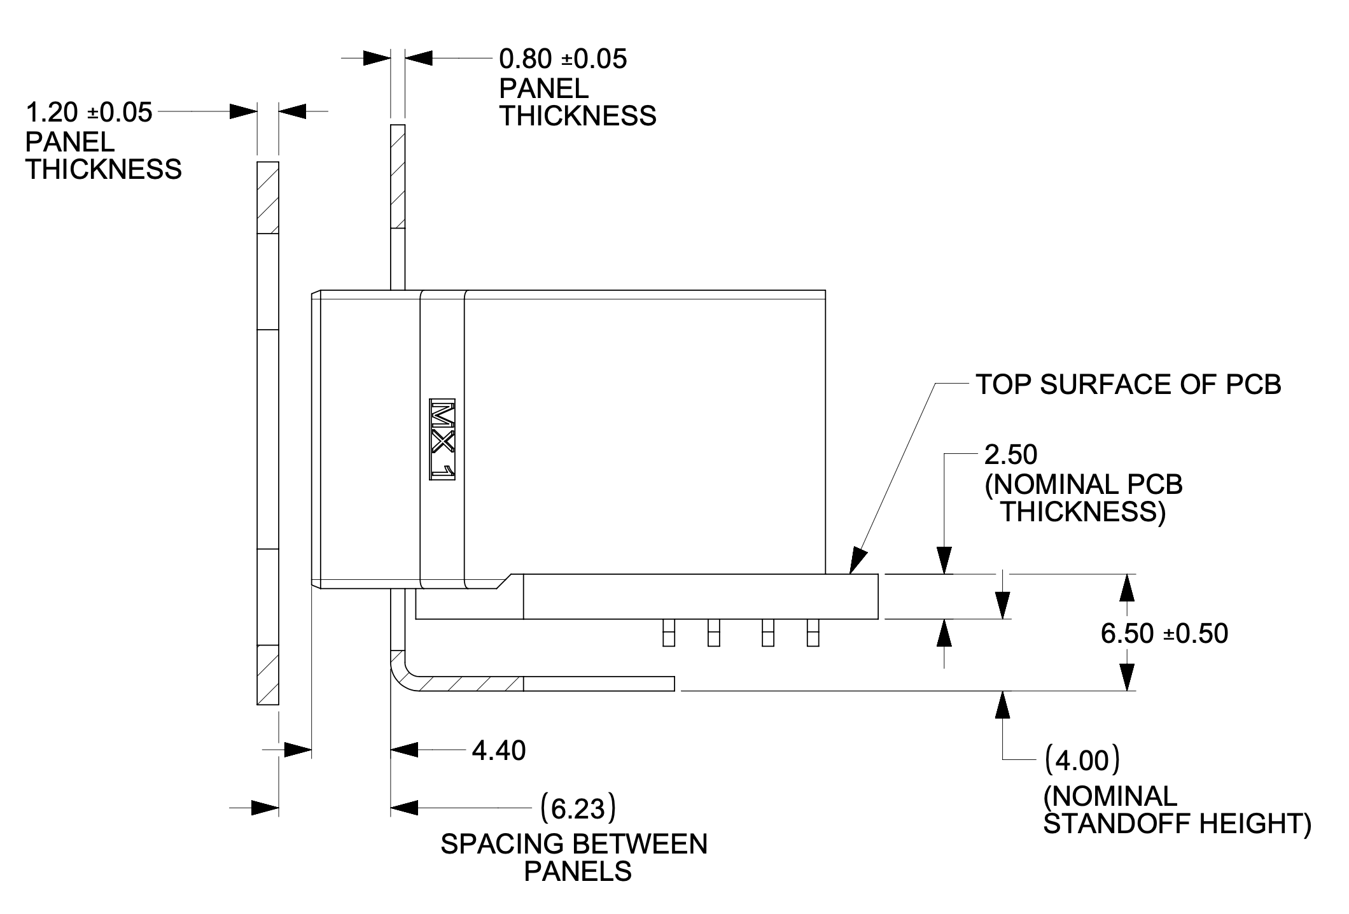
images/power/brick_power_connector_panel_location.png
