Green-Software-Foundation/open19/images/power/open19_brick_supply_return_layout.png

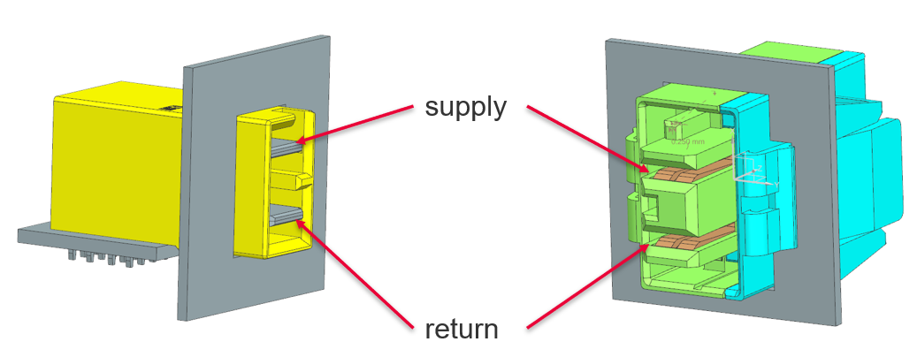
images/power/open19_brick_supply_return_layout.png
