Green-Software-Foundation/open19/images/power/power_shelf_connector_with_panel_upper.png

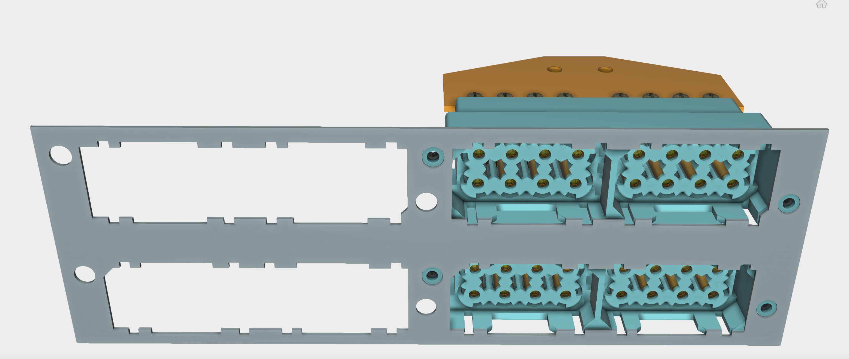
images/power/power_shelf_connector_with_panel_upper.png
