Green-Software-Foundation/open19/images/SSI-vertical.png

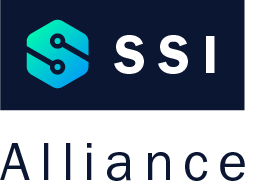
images/SSI-vertical.png
