Green-Software-Foundation/open19/images/Table 1 - Data Connector Pinout for Specialty Switch.jpg

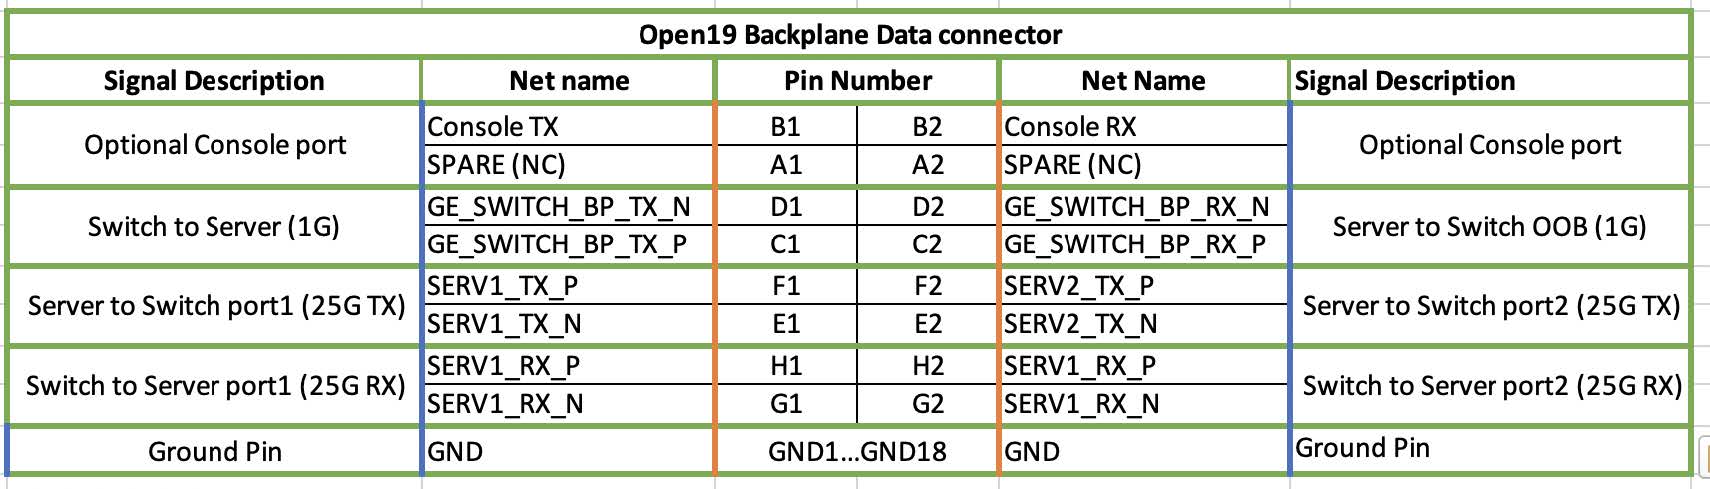
images/Table 1 - Data Connector Pinout for Specialty Switch.jpg
