Green-Software-Foundation/open19/power/brick_power_connection_with_panel_with_key_and_updated_panel.stp_1.png

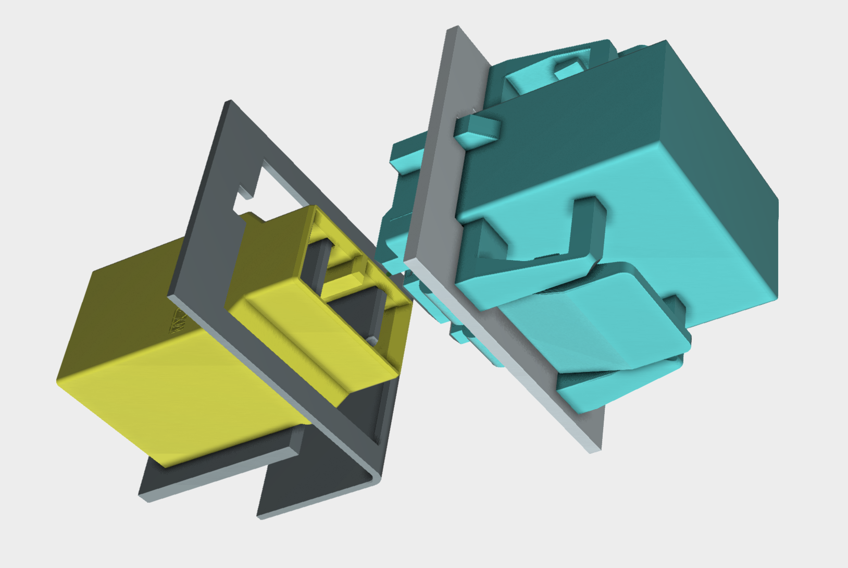
power/brick_power_connection_with_panel_with_key_and_updated_panel.stp_1.png
