Green-Software-Foundation/open19/images/chapters/ch_brick_mechanical/shdw_brick_mechanical_guide.png

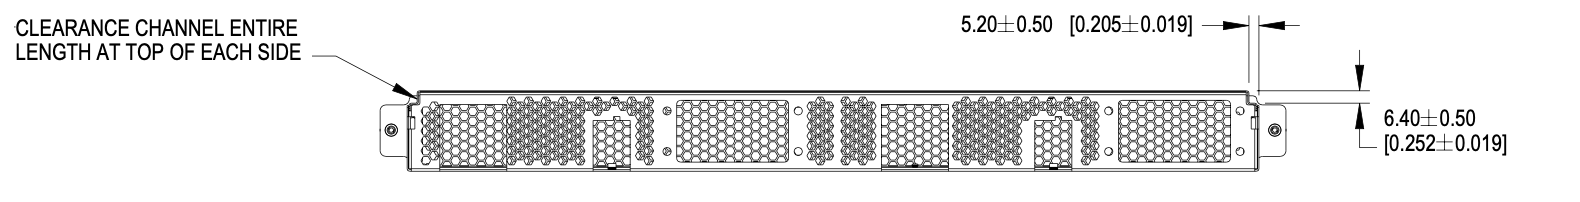
images/chapters/ch_brick_mechanical/shdw_brick_mechanical_guide.png
