Green-Software-Foundation/open19/implementer_notes/csco/cisco-cS-o19v2-stackup.pdf

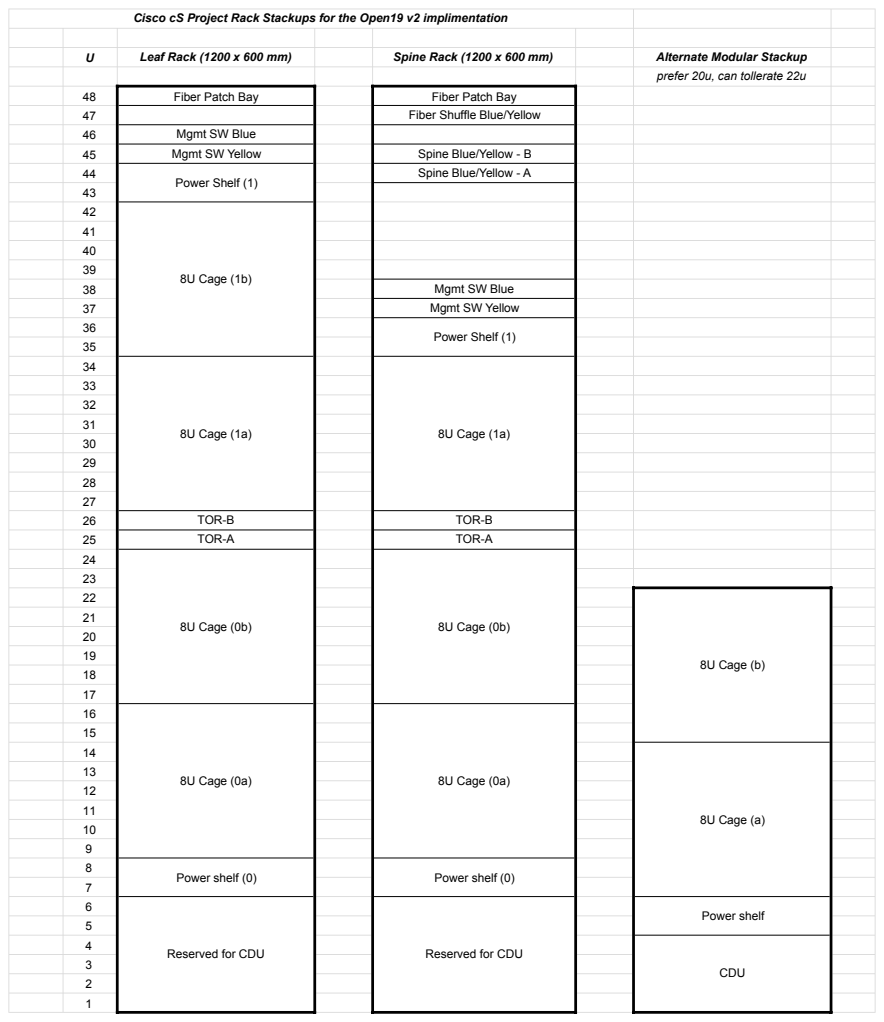
[picture p364: page 1]
Leaf Rack (1200 x 600 mm); Spine Rack (1200 x 600 mm); Alternate Modular Stackup; Fiber Patch Bay; Fiber Shuffle Blue/Yellow; Mgmt SW Blue; Mgmt SW Yellow; Spine Blue/Yellow - B; Power Shelf (1); 8U Cage (1b); 8U Cage (1a); TOR-B; TOR-A; 8U Cage (0b); 8U Cage (b); 8U Cage (0a); 8U Cage (a); Power shelf (0); Reserved for CDU; Power shelf; CDU 3

Cisco cS Project Rack Stackups for the Open19 v2 implimentation

prefer 20u, can tollerate 22u

Spine Blue/Yellow - A
