Green-Software-Foundation/open19/implementer_notes/eqix/Equinix_Open19_V2_Elevations.pdf

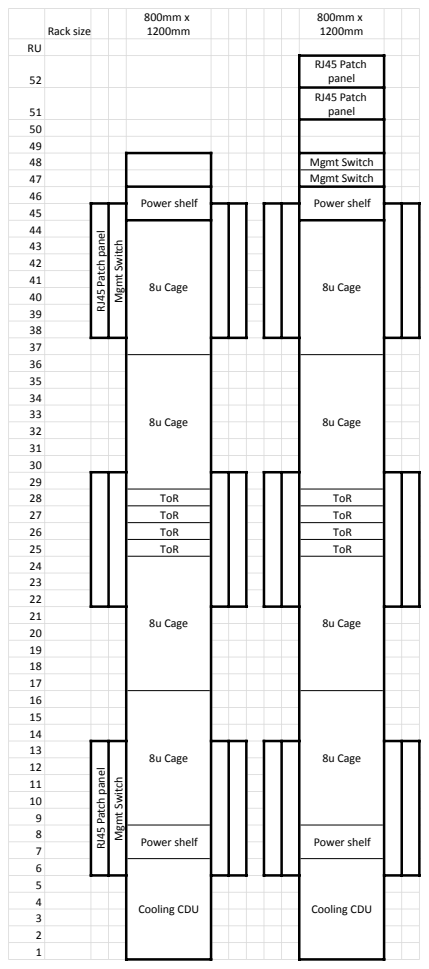
[picture p365: page 1]
Rack size; RJ45 Patch panel; Mgmt Switch; Power shelf; 8u Cage; ToR; Power shelf 76; Cooling CDU
