Green-Software-Foundation/open19/power/2203680000_sd_pg2.pdf

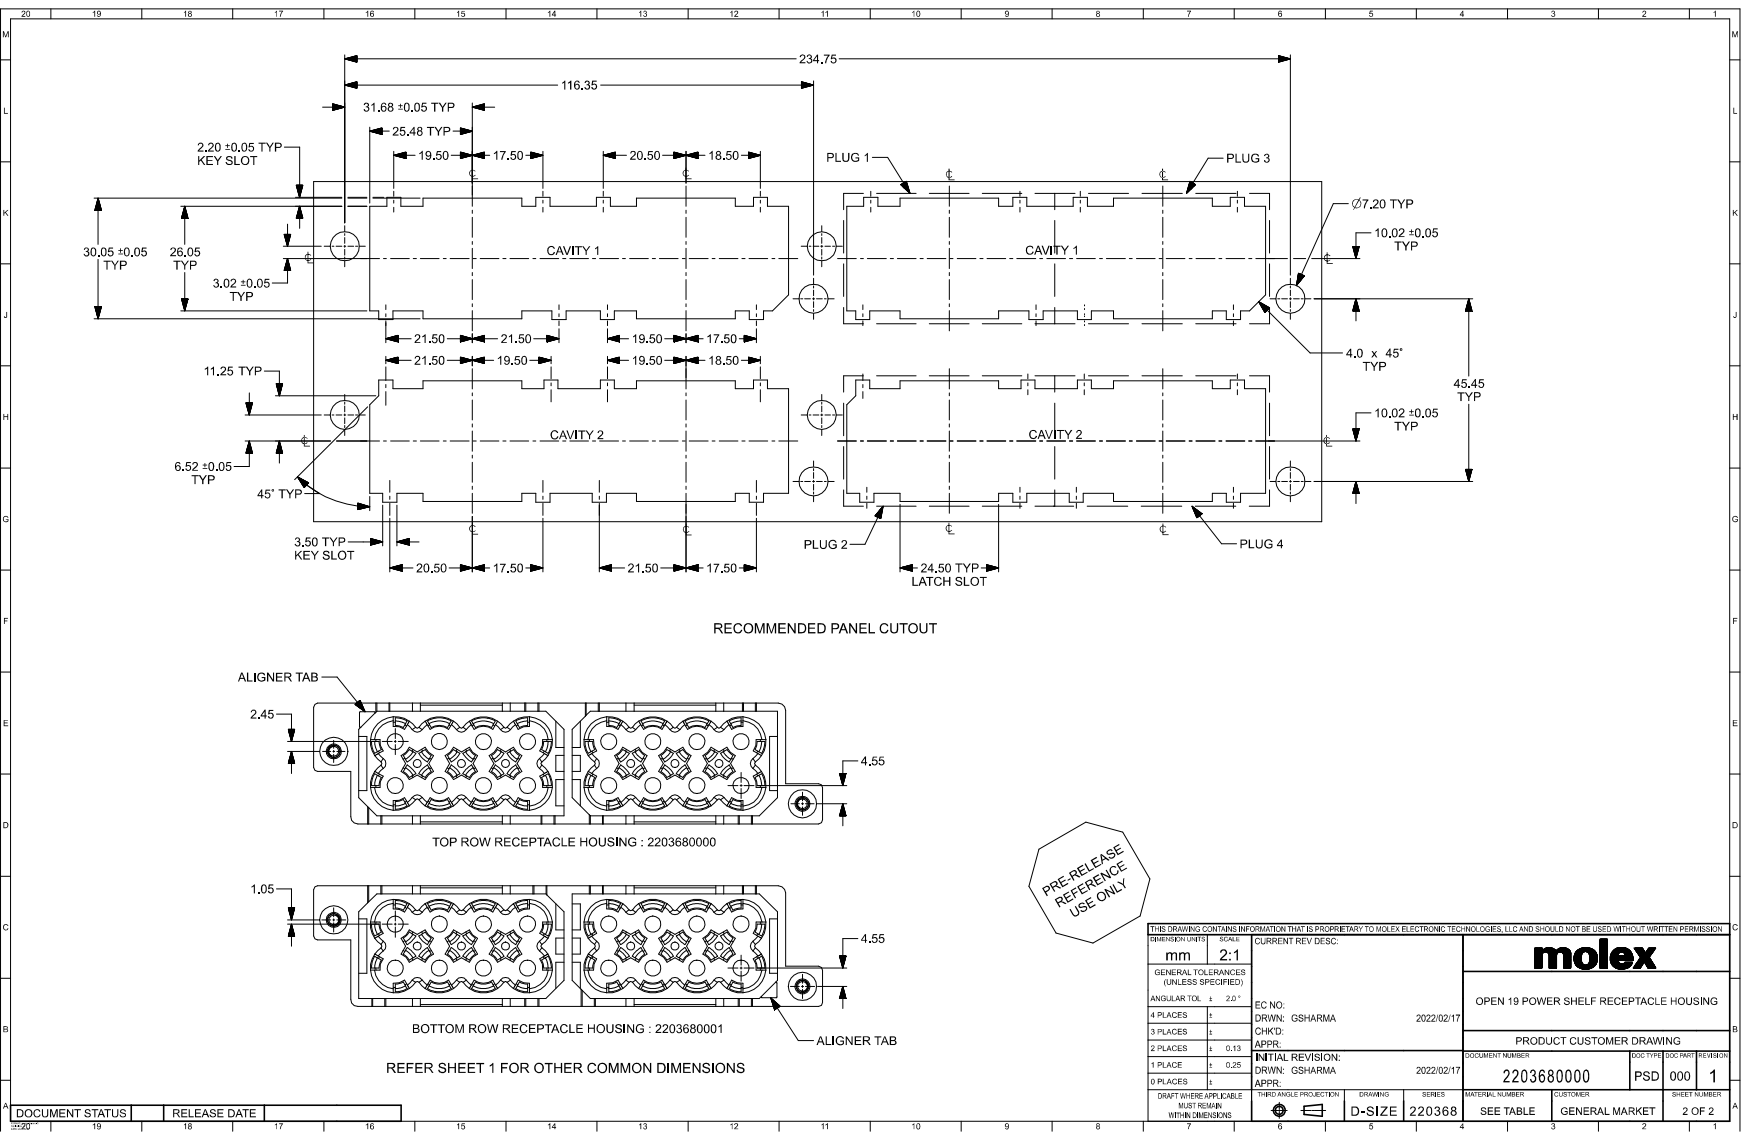
[picture p369: page 1]
