Green-Software-Foundation/open19/power/Open19V2_Power_Connector_Brick_Map.pdf

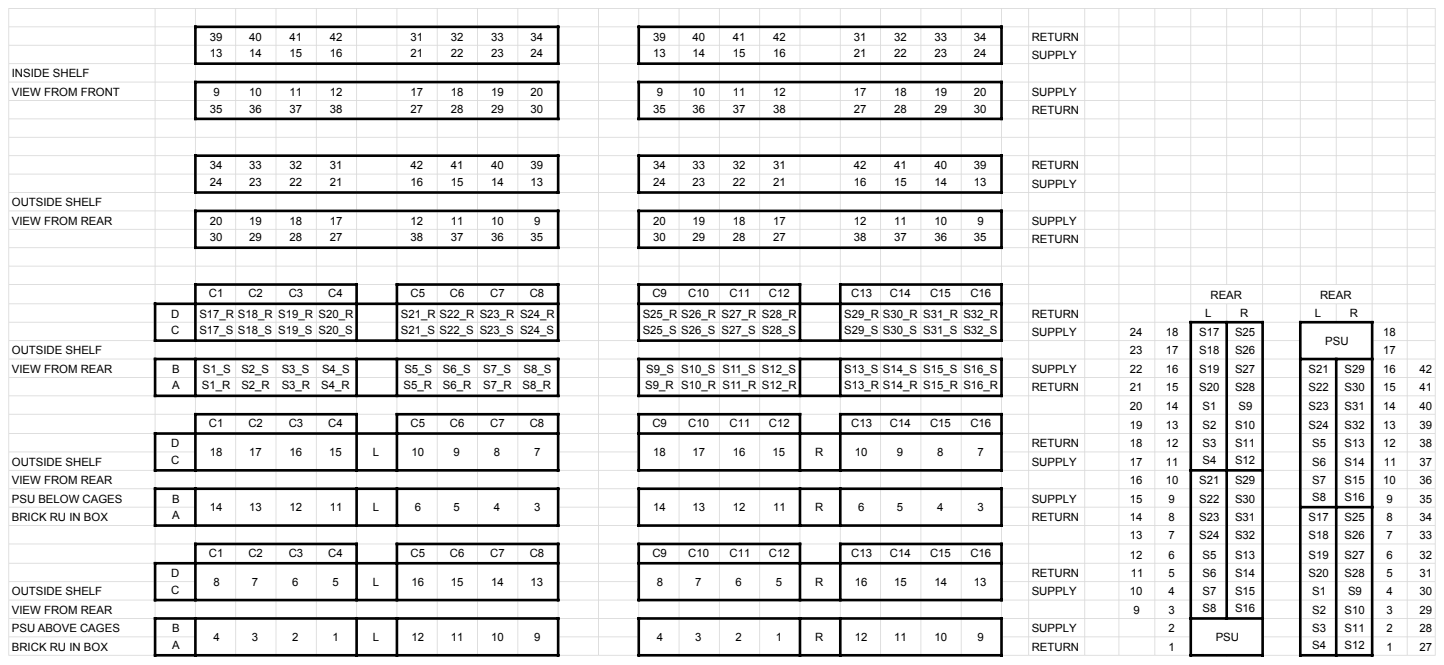
[picture p370: page 1]
