Green-Software-Foundation/open19/implementer_notes/molex/2203940032-sdpsd000_01.pdf

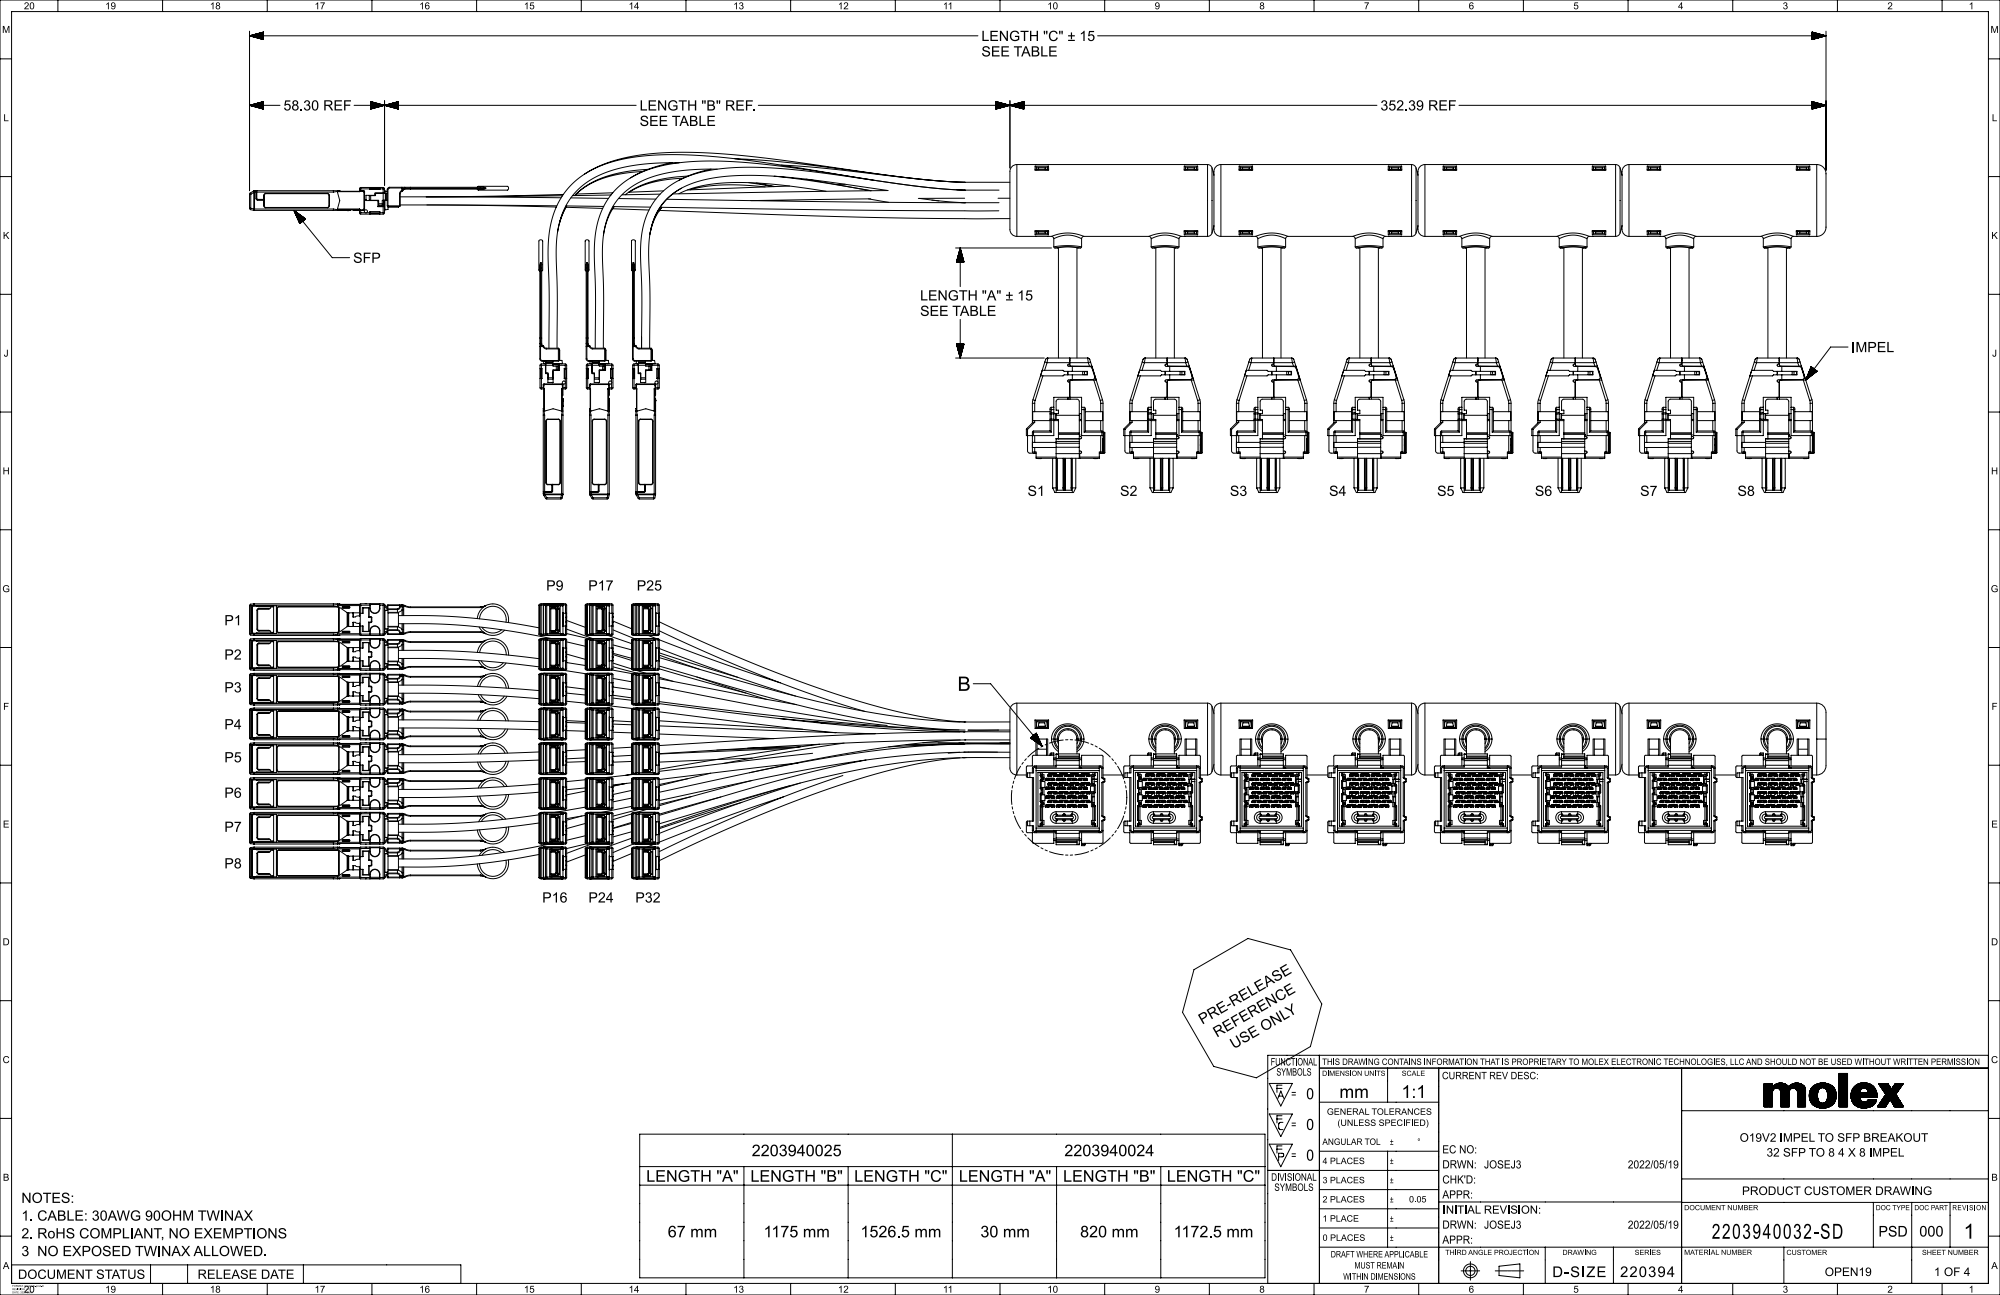
[picture p371: page 1]

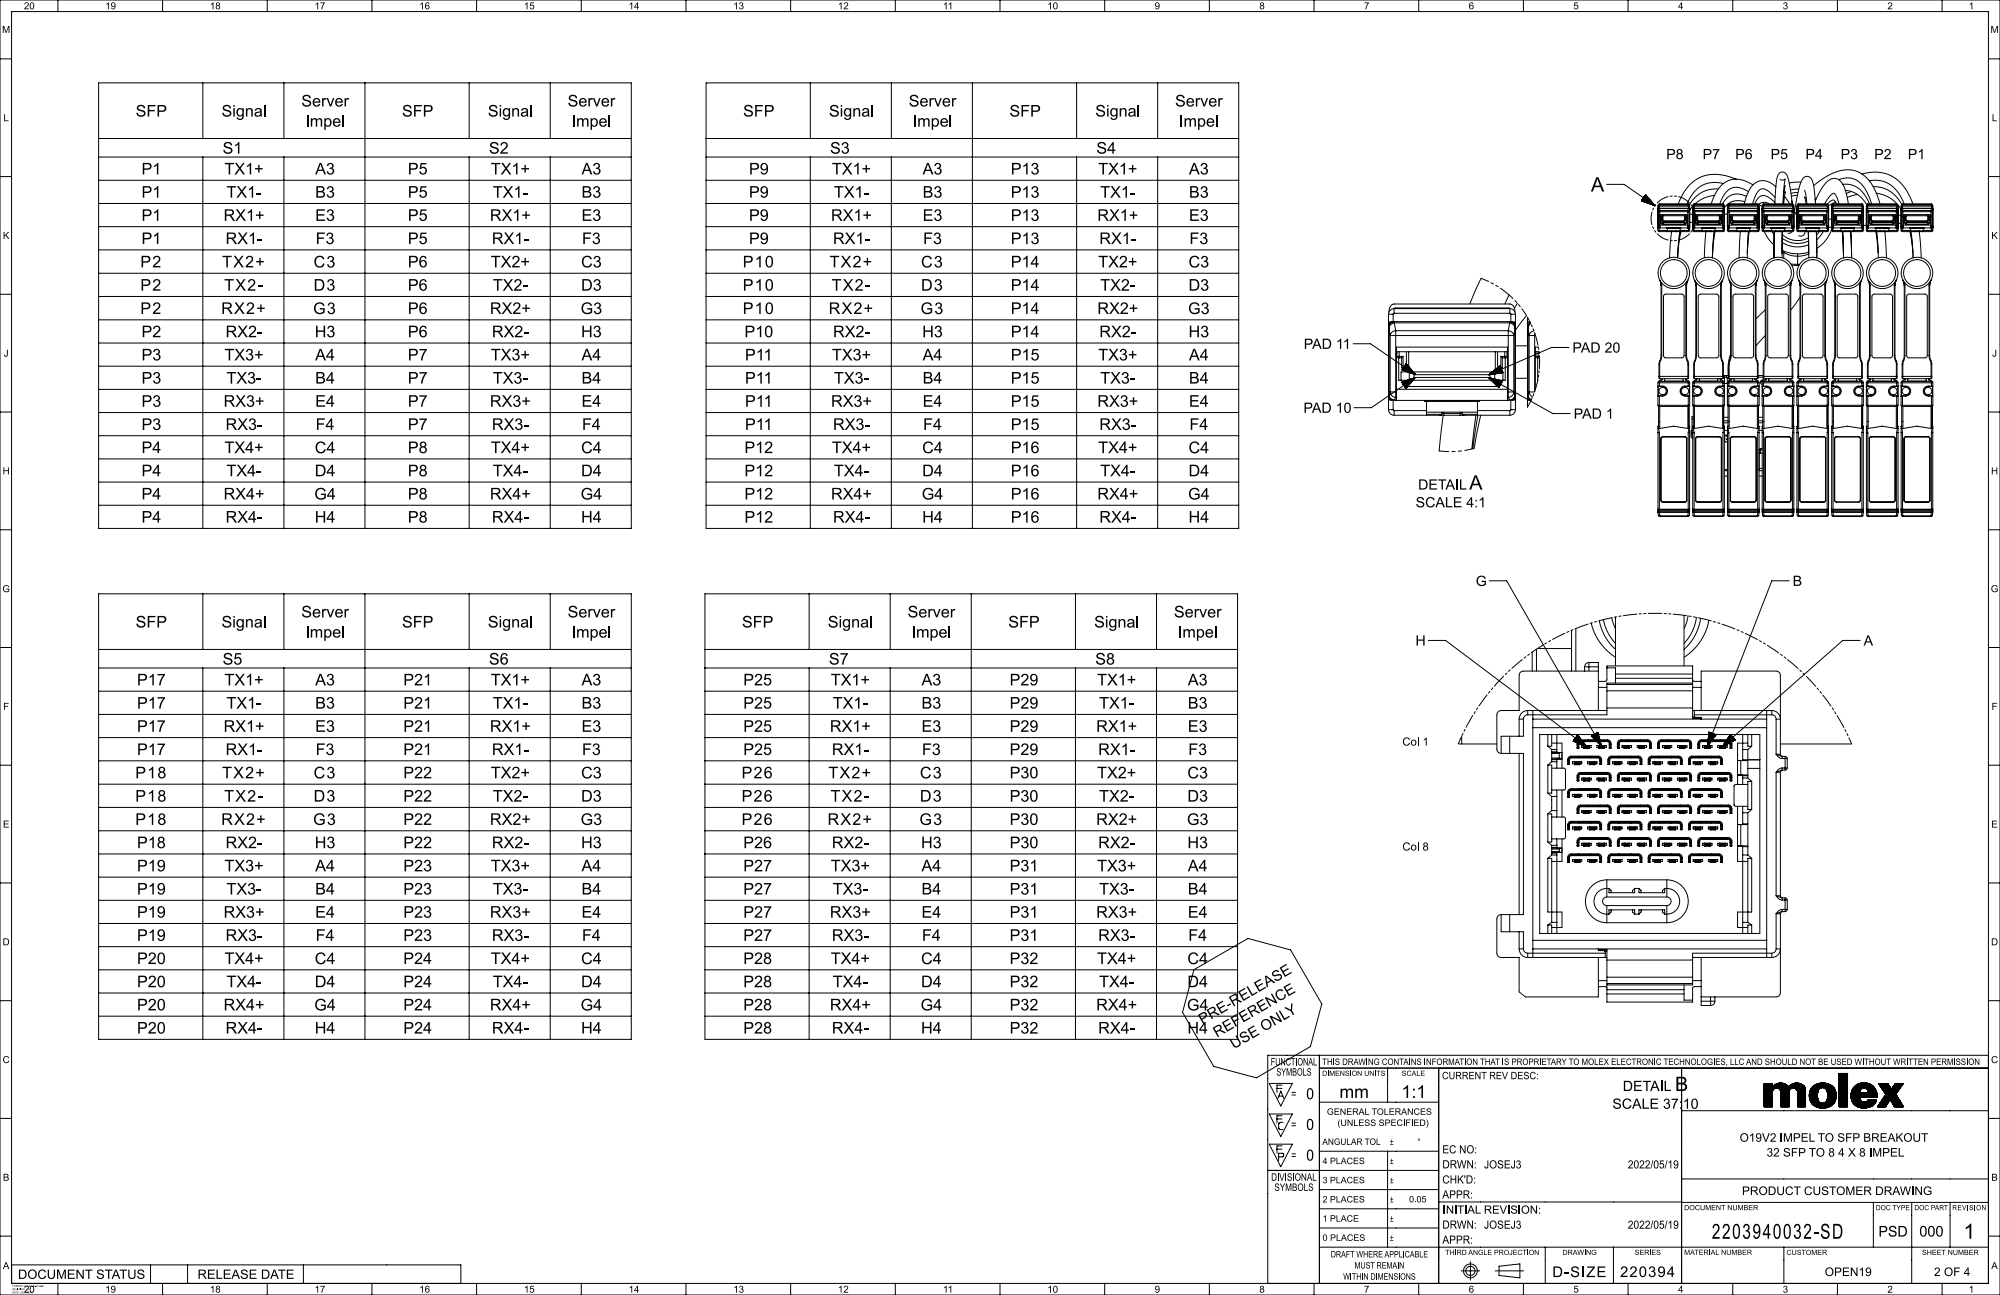
[picture p372: page 2]

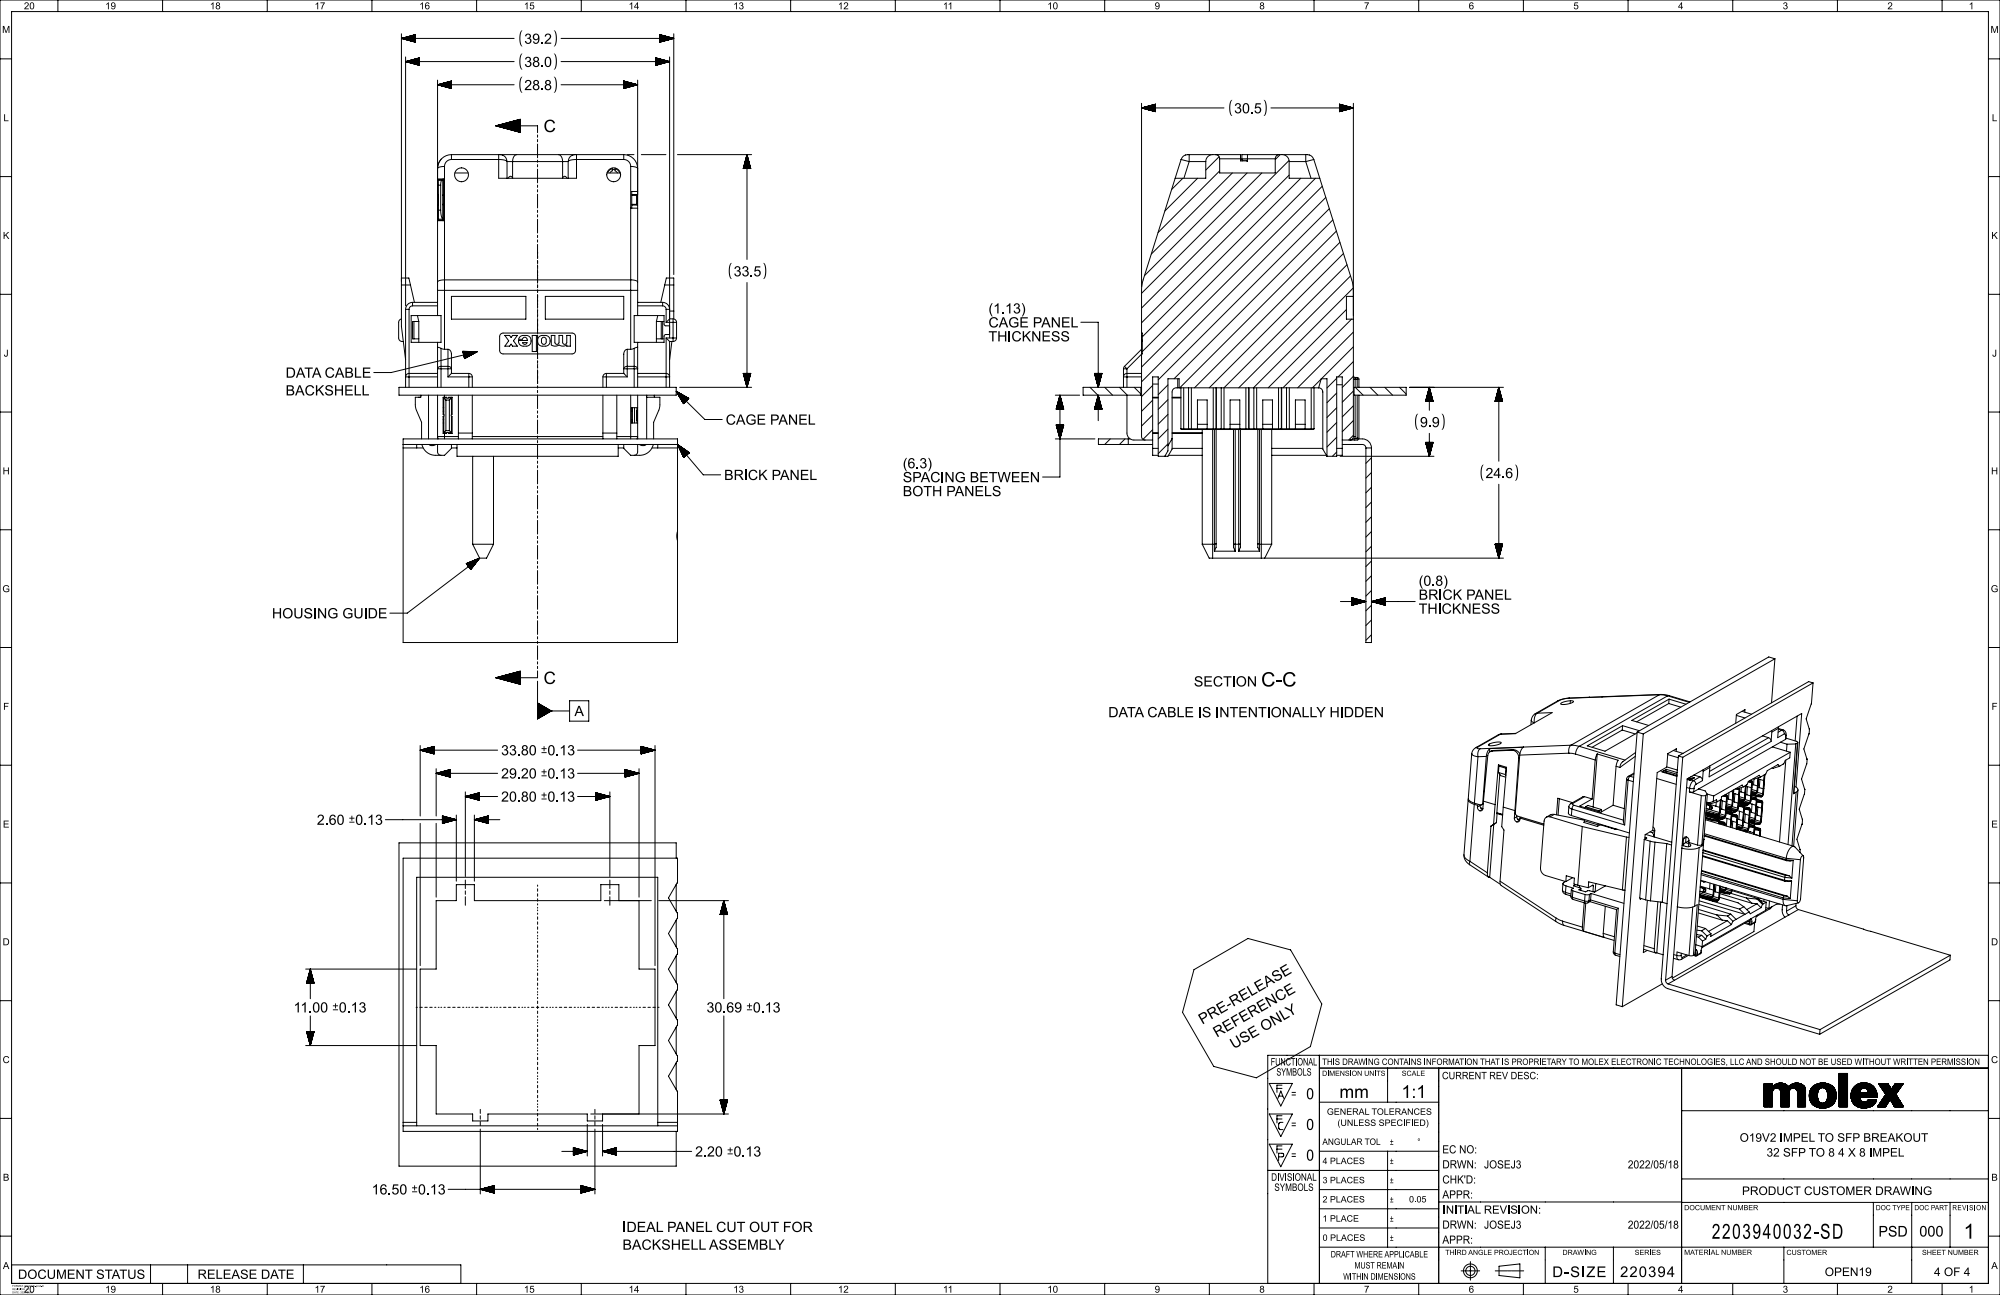
[picture p373: page 3]

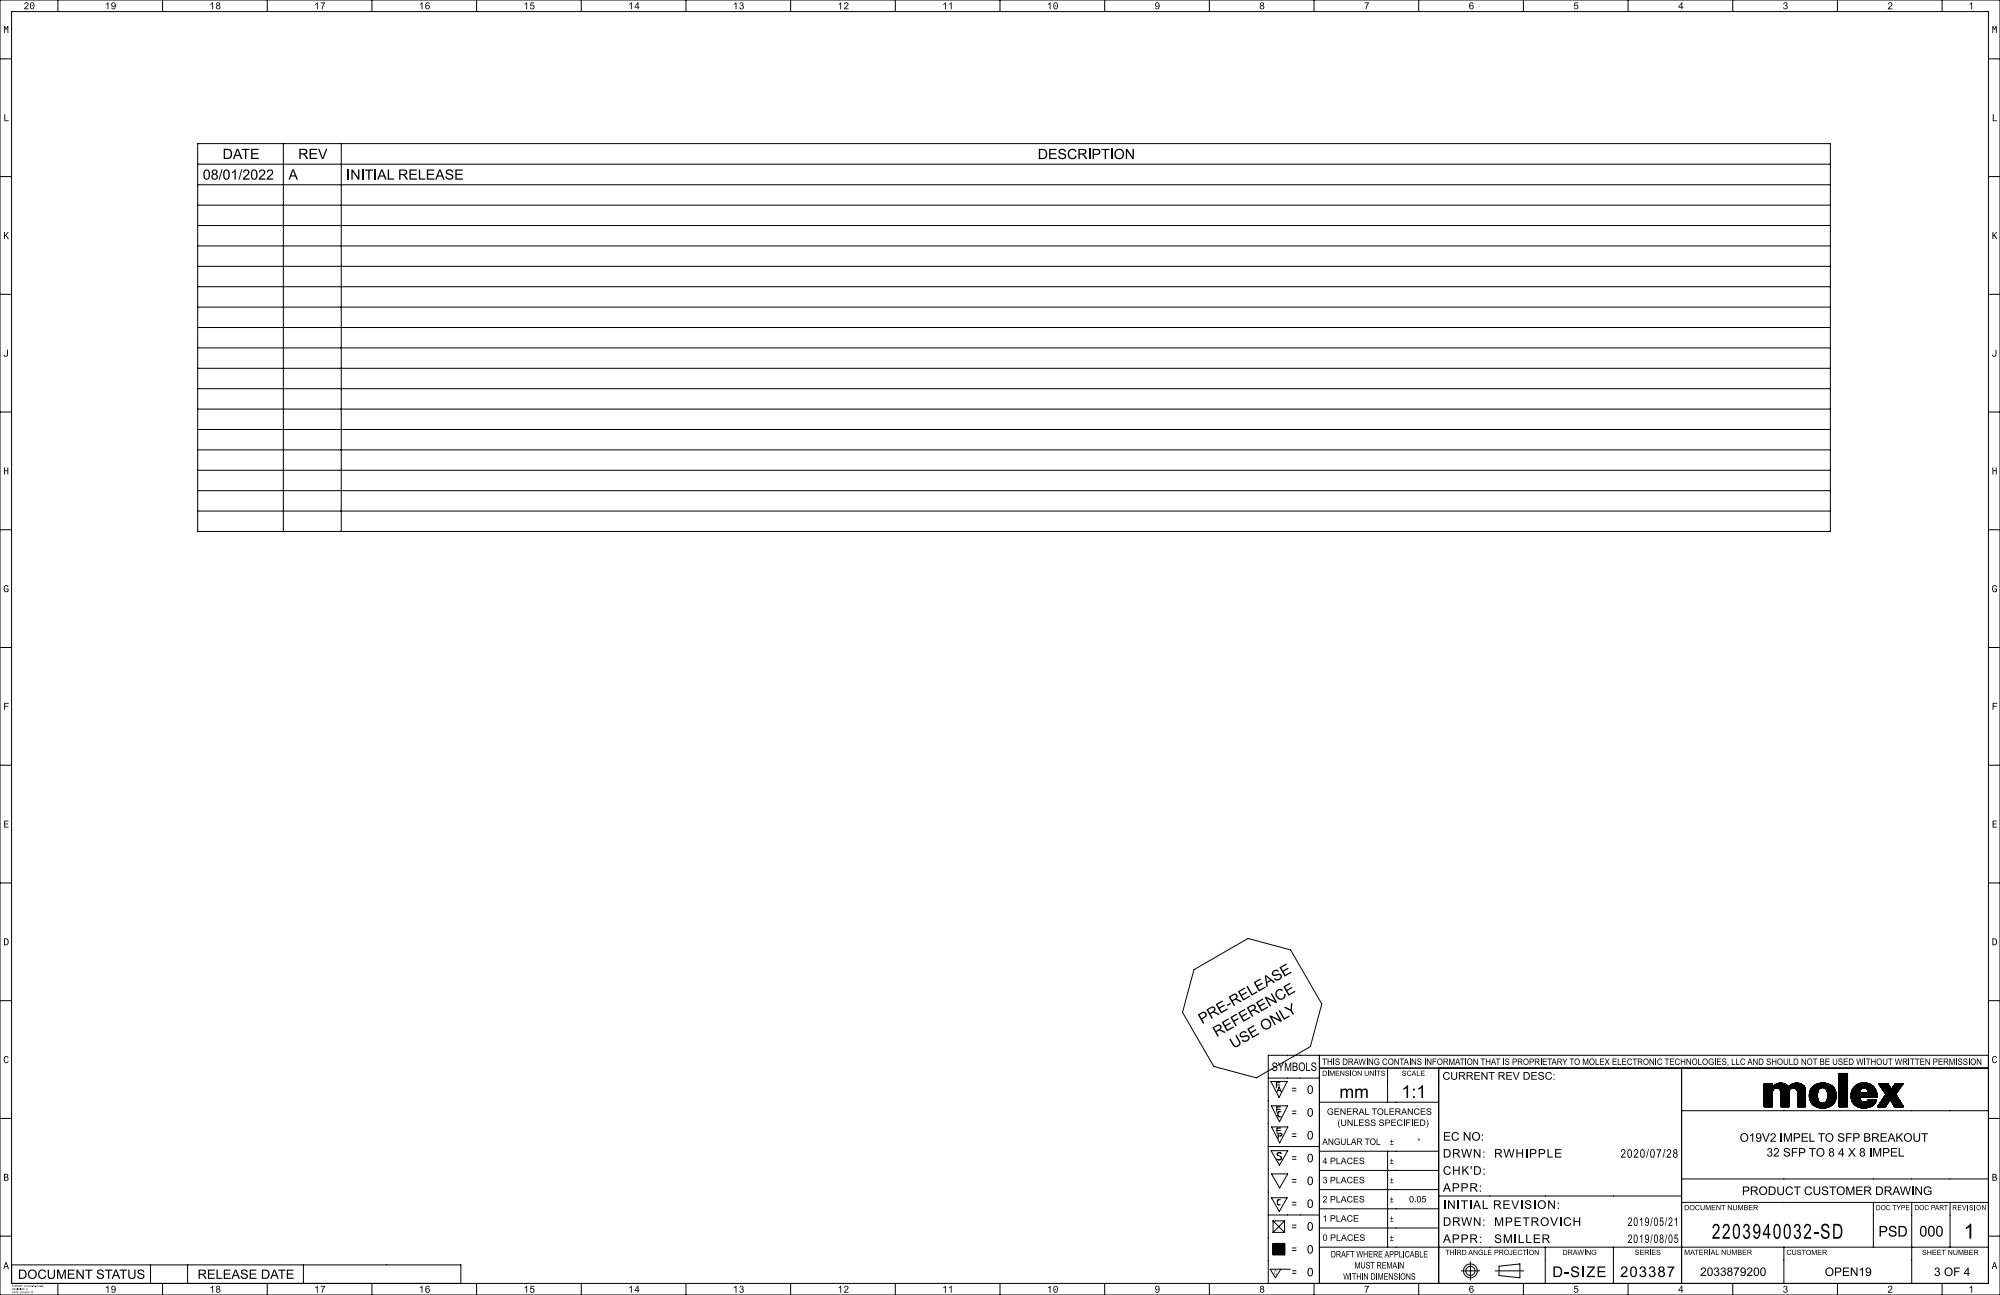
[picture p374: page 4]
